smartuni/riot-po-2025/nodes/firmware/custom-modules/tables/tables.c

#include "include/tables.h"
#include <stdatomic.h>
#include <stdio.h>
#include <string.h>
#include <stdint.h>
#include "mutex.h"
#include <stddef.h>
#include "embUnit.h"
#include "embUnit/embUnit.h"
#include "fmt.h"
#include "cbor.h"
#include "container.h"
#include "atomic_utils.h"


// Return Codes
#define TABLE_ERROR_SIZE_TOO_BIG -1
#define TABLE_ERROR_INVALID_GATE_ID -2
#define TABLE_ERROR_NOT_FOUND   -3

// Static tables
static target_state_entry target_state_entry_table[MAX_GATE_COUNT];
static int target_state_entry_count = 0;
static is_state_entry is_state_entry_table[MAX_GATE_COUNT];
static int is_state_entry_count = 0;
static seen_status_entry seen_status_entry_table[MAX_GATE_COUNT][MAX_SENSE_COUNT];
static int seen_status_entry_count = 0;
static jobs_entry jobs_entry_table[MAX_GATE_COUNT];
static int jobs_entry_count = 0;
static timestamp_entry timestamp_table[MAX_GATE_COUNT];
static int timestamp_entry_count = 0;

static target_state_entry returnTargetTable[MAX_GATE_COUNT];
static is_state_entry returnIsTable[MAX_GATE_COUNT];
static seen_status_entry returnSeenTable[MAX_GATE_COUNT];
static jobs_entry returnJobsTable[MAX_GATE_COUNT];

// Mutexes for thread safety
static mutex_t target_state_mutex = MUTEX_INIT;
static mutex_t is_state_mutex = MUTEX_INIT;
static mutex_t seen_status_mutex = MUTEX_INIT;
static mutex_t jobs_mutex = MUTEX_INIT;
static mutex_t timestamp_mutex = MUTEX_INIT;
static mutex_t decode_mutex = MUTEX_INIT;

static volatile uint32_t device_timestamp = 0;

void increment_device_timestamp(void) {
    atomic_fetch_add_u32(&device_timestamp, 1);
}

uint32_t increment_and_get_device_timestamp(void) {
    return atomic_fetch_add_u32(&device_timestamp, 1);
}

uint32_t get_device_timestamp(void) {
    return atomic_load_u32(&device_timestamp);
}

/**
 * Initialize all tables with default values
 */
int init_tables(void) {
    mutex_lock(&target_state_mutex);
    mutex_lock(&is_state_mutex);
    mutex_lock(&seen_status_mutex);
    mutex_lock(&jobs_mutex);
    mutex_lock(&timestamp_mutex);
    
    for (int i = 0; i < MAX_GATE_COUNT; i++) {
        target_state_entry_table[i].gateID = MAX_GATE_COUNT;  // Mark as empty
        is_state_entry_table[i].gateID = MAX_GATE_COUNT;
        jobs_entry_table[i].gateID = MAX_GATE_COUNT;
        timestamp_table[i].gateID = MAX_GATE_COUNT;
    }

    for (int i = 0; i < MAX_GATE_COUNT; i++) {
        for (int j = 0; j < MAX_SENSE_COUNT; j++) {
            seen_status_entry_table[i][j].gateID = MAX_GATE_COUNT;
            seen_status_entry_table[i][j].senseMateID = MAX_SENSE_COUNT;
        }
    }
    
    mutex_unlock(&timestamp_mutex);
    mutex_unlock(&jobs_mutex);
    mutex_unlock(&seen_status_mutex);
    mutex_unlock(&is_state_mutex);
    mutex_unlock(&target_state_mutex);
    
    return TABLE_SUCCESS;
}

static int is_target_state_entry_present_internal(uint8_t gate_id) {
    if (gate_id >= MAX_GATE_COUNT) {
        return 0;  // Invalid gate_id = not present
    }
    uint8_t entry_gate_id = target_state_entry_table[gate_id].gateID;
    return entry_gate_id != MAX_GATE_COUNT && entry_gate_id == gate_id;
}

static int is_is_state_entry_present_internal(uint8_t gate_id) {
    if (gate_id >= MAX_GATE_COUNT) {
        return 0;
    }
    uint8_t entry_gate_id = is_state_entry_table[gate_id].gateID;
    return entry_gate_id != MAX_GATE_COUNT && entry_gate_id == gate_id;
}

static int is_seen_status_entry_present_internal(uint8_t gate_id, uint8_t sense_id) {
    if (gate_id >= MAX_GATE_COUNT || sense_id >= MAX_SENSE_COUNT) {
        return 0;
    }
    seen_status_entry entry = seen_status_entry_table[gate_id][sense_id];
    return entry.gateID != MAX_GATE_COUNT 
            && entry.gateID == gate_id 
            && entry.senseMateID != MAX_SENSE_COUNT 
            && entry.senseMateID == sense_id;
}

static int is_jobs_entry_present_internal(uint8_t gate_id) {
    if (gate_id >= MAX_GATE_COUNT) {
        return 0;
    }
    uint8_t entry_gate_id = jobs_entry_table[gate_id].gateID;
    return entry_gate_id != MAX_GATE_COUNT && entry_gate_id == gate_id;
}

static int is_timestamp_entry_present_internal(uint8_t gate_id) {
    if (gate_id >= MAX_GATE_COUNT) {
        return 0;
    }
    uint8_t entry_gate_id = timestamp_table[gate_id].gateID;
    return entry_gate_id != MAX_GATE_COUNT && entry_gate_id == gate_id;
}



static inline int is_valid_gate_id(uint8_t gate_id) {
    return gate_id < MAX_GATE_COUNT;
}

int target_state_table_to_cbor_test(target_state_entry table[], cbor_buffer* buffer) {
    CborEncoder encoder, arrayEncoder, entriesEncoder, singleEntryEncoder;
    cbor_encoder_init(&encoder, buffer->buffer, sizeof(uint8_t) * 100, 0);
    cbor_encoder_create_array(&encoder, &arrayEncoder, 3); // [
    cbor_encode_int(&arrayEncoder, TARGET_STATE_KEY); // Entry 1
    cbor_encode_int(&arrayEncoder, 2008); // Entry 2
    cbor_encoder_create_array(&arrayEncoder, &entriesEncoder, 4); // Entry 3

    // [Table Entry]
    for(int i = 0; i < 4; i++) {
        if (table[i].gateID != MAX_GATE_COUNT) {
            cbor_encoder_create_array(&entriesEncoder, &singleEntryEncoder, 3); // []
            cbor_encode_int(&singleEntryEncoder, table[i].gateID);
            cbor_encode_int(&singleEntryEncoder, table[i].state);
            cbor_encode_int(&singleEntryEncoder, table[i].timestamp);
            cbor_encoder_close_container(&entriesEncoder, &singleEntryEncoder); // ]
        }
    }

    cbor_encoder_close_container(&arrayEncoder, &entriesEncoder); // ]
    cbor_encoder_close_container(&encoder, &arrayEncoder); // ]

    buffer->cbor_size = (uint8_t) cbor_encoder_get_buffer_size (&encoder, buffer->buffer);

    return 0;
}

int target_state_table_to_cbor(cbor_buffer* buffer) {
    if (target_state_entry_count == 0){
        return -1; // No entries in table
    }
    CborEncoder encoder, arrayEncoder, entriesEncoder, singleEntryEncoder;
    cbor_encoder_init(&encoder, buffer->buffer, sizeof(uint8_t) * 100, 0);
    cbor_encoder_create_array(&encoder, &arrayEncoder, 2); // [
    cbor_encode_int(&arrayEncoder, TARGET_STATE_KEY); // Entry 1
    cbor_encoder_create_array(&arrayEncoder, &entriesEncoder, target_state_entry_count); // Entry 2

    // [Table Entry]
    for(int i = 0; i < MAX_GATE_COUNT; i++) {
        if (is_target_state_entry_present_internal(i)) {
            cbor_encoder_create_array(&entriesEncoder, &singleEntryEncoder, 3); // []
            cbor_encode_int(&singleEntryEncoder, target_state_entry_table[i].gateID);
            cbor_encode_int(&singleEntryEncoder, target_state_entry_table[i].state);
            cbor_encode_int(&singleEntryEncoder, target_state_entry_table[i].timestamp);
            cbor_encoder_close_container(&entriesEncoder, &singleEntryEncoder); // ]
        }
    }

    cbor_encoder_close_container(&arrayEncoder, &entriesEncoder); // ]
    cbor_encoder_close_container(&encoder, &arrayEncoder); // ]

    buffer->cbor_size =  (uint8_t) cbor_encoder_get_buffer_size (&encoder, buffer->buffer);

    return 0;
}

int is_state_table_to_cbor(cbor_buffer* buffer) {
    if (is_state_entry_count == 0){
        return -1; // No entries in table
    }
    CborEncoder encoder, arrayEncoder, entriesEncoder, singleEntryEncoder;
    cbor_encoder_init(&encoder, buffer->buffer, sizeof(uint8_t) * 100, 0);
    cbor_encoder_create_array(&encoder, &arrayEncoder, 2); // [
    cbor_encode_int(&arrayEncoder, TARGET_STATE_KEY); // Entry 1
    cbor_encoder_create_array(&arrayEncoder, &entriesEncoder, is_state_entry_count); // Entry 2

    // [Table Entry]
    for(int i = 0; i < MAX_GATE_COUNT; i++) {
        if(is_is_state_entry_present_internal(i)) {
            cbor_encoder_create_array(&entriesEncoder, &singleEntryEncoder, 3); // []
            cbor_encode_int(&singleEntryEncoder, is_state_entry_table[i].gateID);
            cbor_encode_int(&singleEntryEncoder, is_state_entry_table[i].state);
            cbor_encode_int(&singleEntryEncoder, is_state_entry_table[i].gateTime);
            cbor_encoder_close_container(&entriesEncoder, &singleEntryEncoder); // ]
        }
    }

    cbor_encoder_close_container(&arrayEncoder, &entriesEncoder); // ]
    cbor_encoder_close_container(&encoder, &arrayEncoder); // ]

    buffer->cbor_size =  (uint8_t) cbor_encoder_get_buffer_size (&encoder, buffer->buffer);

    return 0;
}

int seen_status_table_to_cbor(cbor_buffer* buffer) {
    if (seen_status_entry_count == 0){
        return -1; // No entries in table
    }
    CborEncoder encoder, arrayEncoder, entriesEncoder, singleEntryEncoder;
    cbor_encoder_init(&encoder, buffer->buffer, sizeof(uint8_t) * 100, 0);
    cbor_encoder_create_array(&encoder, &arrayEncoder, 2); // [
    cbor_encode_int(&arrayEncoder, TARGET_STATE_KEY); // Entry 1
    cbor_encoder_create_array(&arrayEncoder, &entriesEncoder, seen_status_entry_count); // Entry 2

    // [Table Entry]
    for(int i = 0; i < MAX_GATE_COUNT; i++) {
        for (int j = 0; j < MAX_SENSE_COUNT; j++) {
            if(is_seen_status_entry_present_internal(i, j)) {
                cbor_encoder_create_array(&entriesEncoder, &singleEntryEncoder, 3); // []
                cbor_encode_int(&singleEntryEncoder, seen_status_entry_table[i][j].gateID);
                cbor_encode_int(&singleEntryEncoder, seen_status_entry_table[i][j].gateTime);
                cbor_encode_int(&singleEntryEncoder, seen_status_entry_table[i][j].status);
                cbor_encode_int(&singleEntryEncoder, seen_status_entry_table[i][j].senseMateID);
                cbor_encoder_close_container(&entriesEncoder, &singleEntryEncoder); // ]
            }
        }
    }

    cbor_encoder_close_container(&arrayEncoder, &entriesEncoder); // ]
    cbor_encoder_close_container(&encoder, &arrayEncoder); // ]

    buffer->cbor_size =  (uint8_t) cbor_encoder_get_buffer_size (&encoder, buffer->buffer);

    return 0;
}

int jobs_table_to_cbor(cbor_buffer* buffer) {
    if (jobs_entry_count == 0){
        return -1; // No jobs in table
    }
    CborEncoder encoder, arrayEncoder, entriesEncoder, singleEntryEncoder;
    cbor_encoder_init(&encoder, buffer->buffer, sizeof(uint8_t) * 100, 0);
    cbor_encoder_create_array(&encoder, &arrayEncoder, 2); // [
    cbor_encode_int(&arrayEncoder, TARGET_STATE_KEY); // Entry 1
    cbor_encoder_create_array(&arrayEncoder, &entriesEncoder, jobs_entry_count); // Entry 2

    // [Table Entry]
    for(int i = 0; i < MAX_GATE_COUNT; i++) {
        if (is_jobs_entry_present_internal(i)) {
            cbor_encoder_create_array(&entriesEncoder, &singleEntryEncoder, 3); // []
            cbor_encode_int(&singleEntryEncoder, jobs_entry_table[i].gateID);
            cbor_encode_int(&singleEntryEncoder, jobs_entry_table[i].done);
            cbor_encoder_close_container(&entriesEncoder, &singleEntryEncoder); // ]
        }
    }

    cbor_encoder_close_container(&arrayEncoder, &entriesEncoder); // ]
    cbor_encoder_close_container(&encoder, &arrayEncoder); // ]

    buffer->cbor_size =  (uint8_t) cbor_encoder_get_buffer_size (&encoder, buffer->buffer);

    return 0;
}

int timestamp_table_to_cbor(cbor_buffer* buffer) {
    if (timestamp_entry_count == 0){
        return -1; // No jobs in table
    }
    CborEncoder encoder, arrayEncoder, entriesEncoder, singleEntryEncoder;
    cbor_encoder_init(&encoder, buffer->buffer, sizeof(uint8_t) * 100, 0);
    cbor_encoder_create_array(&encoder, &arrayEncoder, 2); // [
    cbor_encode_int(&arrayEncoder, TIMESTAMP_KEY); // Entry 1
    cbor_encoder_create_array(&arrayEncoder, &entriesEncoder, timestamp_entry_count); // Entry 2

    // [Table Entry]
    for(int i = 0; i < MAX_GATE_COUNT; i++) {
        if (is_jobs_entry_present_internal(i)) {
            cbor_encoder_create_array(&entriesEncoder, &singleEntryEncoder, 3); // []
            cbor_encode_int(&singleEntryEncoder, timestamp_table[i].gateID);
            cbor_encode_int(&singleEntryEncoder, timestamp_table[i].timestamp);
            cbor_encode_int(&singleEntryEncoder, timestamp_table[i].rssi);
            cbor_encoder_close_container(&entriesEncoder, &singleEntryEncoder); // ]
        }
    }

    cbor_encoder_close_container(&arrayEncoder, &entriesEncoder); // ]
    cbor_encoder_close_container(&encoder, &arrayEncoder); // ]

    buffer->cbor_size =  (uint8_t) cbor_encoder_get_buffer_size (&encoder, buffer->buffer);

    return 0;
}

 int print_target_table_test(void){
    printf("\n--- TARGET STATE TABLE ---\n");
    
    for (int i = 0; i < MAX_GATE_COUNT; i++) {
        if (target_state_entry_table[i].gateID!= MAX_GATE_COUNT) { // Entry ist valid
            printf("Gate: %d, State: %d, Time: %d\n", target_state_entry_table[i].gateID, target_state_entry_table[i].state, target_state_entry_table[i].timestamp);
        }
    }
    return 1;
}


int cbor_to_table_test(cbor_buffer* buffer, int8_t rssi) {
    CborParser parser;
    CborValue value;
    CborValue wrapperValue;
    CborValue fieldsValue;
    CborValue entryValue;
    mutex_lock(&decode_mutex);
    int tableType, timeStamp, typeOfSender, deviceID;
    memset(returnTargetTable, MAX_GATE_COUNT, sizeof(returnTargetTable));
    memset(returnIsTable, MAX_GATE_COUNT, sizeof(returnIsTable));
    memset(returnSeenTable, MAX_GATE_COUNT, sizeof(returnSeenTable));
    memset(returnJobsTable, MAX_GATE_COUNT, sizeof(returnJobsTable));

    if (buffer->cbor_size != 1) {
        mutex_unlock(&decode_mutex);
        return -1;
    }

    cbor_parser_init(buffer->buffer, buffer->package_size[0], 0, &parser, &value);

    if(cbor_value_enter_container(&value, &wrapperValue) != CborNoError) {
        mutex_unlock(&decode_mutex);
        return -30;
    }

    if(!cbor_value_is_integer(&wrapperValue) || cbor_value_get_int(&wrapperValue, &tableType) != CborNoError) {
        mutex_unlock(&decode_mutex);
        return -2;
    } // get type of table

    // get header information depending on table type
    switch (tableType)
    {
    case TARGET_STATE_KEY:
        cbor_value_advance(&wrapperValue);
        if(!cbor_value_is_integer(&wrapperValue) || cbor_value_get_int(&wrapperValue, &timeStamp) != CborNoError) {
            mutex_unlock(&decode_mutex);
            return -3;
        } // get timestamp
        cbor_value_advance(&wrapperValue);
        if(!cbor_value_is_integer(&wrapperValue) || cbor_value_get_int(&wrapperValue, &typeOfSender) != CborNoError) {
            mutex_unlock(&decode_mutex);
            return -4;
        } // get whether Sensemate, gate or Server sent msg
        cbor_value_advance(&wrapperValue);
        if(!cbor_value_is_integer(&wrapperValue) || cbor_value_get_int(&wrapperValue, &deviceID) != CborNoError) {
            mutex_unlock(&decode_mutex);
            return -5;
        } // get deviceID
        break;
    case IS_STATE_KEY:
        cbor_value_advance(&wrapperValue);
        if(!cbor_value_is_integer(&wrapperValue) || cbor_value_get_int(&wrapperValue, &timeStamp) != CborNoError) {
            mutex_unlock(&decode_mutex);
            return -6;
        } // get timestamp
        cbor_value_advance(&wrapperValue);
        if(!cbor_value_is_integer(&wrapperValue) || cbor_value_get_int(&wrapperValue, &typeOfSender) != CborNoError) {
            mutex_unlock(&decode_mutex);
            return -7;
        } // get whether Sensemate, gate or Server sent msg
        cbor_value_advance(&wrapperValue);
        if(!cbor_value_is_integer(&wrapperValue) || cbor_value_get_int(&wrapperValue, &deviceID) != CborNoError) {
            mutex_unlock(&decode_mutex);
            return -8;
        } // get deviceID
        break;
    case SEEN_STATUS_KEY:
    cbor_value_advance(&wrapperValue);
        if(!cbor_value_is_integer(&wrapperValue) || cbor_value_get_int(&wrapperValue, &timeStamp) != CborNoError) {
            mutex_unlock(&decode_mutex);
            return -9;
        } // get timestamp
        cbor_value_advance(&wrapperValue);
        if(!cbor_value_is_integer(&wrapperValue) || cbor_value_get_int(&wrapperValue, &typeOfSender) != CborNoError) {
            mutex_unlock(&decode_mutex);
            return -10;
        } // get whether Sensemate, gate or Server sent msg
        cbor_value_advance(&wrapperValue);
        if(!cbor_value_is_integer(&wrapperValue) || cbor_value_get_int(&wrapperValue, &deviceID) != CborNoError) {
            mutex_unlock(&decode_mutex);
            return -11;
        } // get deviceID
        break;
    case JOBS_KEY:
        // no further header information for JOBS table
        break;
    default:
        break;
    }

    // [ enter second container
    cbor_value_advance(&wrapperValue);
    if(cbor_value_enter_container(&wrapperValue, &fieldsValue) != CborNoError) {
        mutex_unlock(&decode_mutex);
        return -12;
    }
    
    int id, s, sID, p, gt;
    size_t length = 0;
    cbor_value_get_array_length(&wrapperValue, &length); 	
    for(size_t i = 0; i < length; i++) {
        cbor_value_enter_container(&fieldsValue, &entryValue); // [
        switch(tableType) {
            case TARGET_STATE_KEY:
                if(!cbor_value_is_integer(&entryValue) || cbor_value_get_int(&entryValue, &id) != CborNoError) {
                    mutex_unlock(&decode_mutex);
                    return -13;
                }
                cbor_value_advance(&entryValue);
                if(!cbor_value_is_integer(&entryValue) || cbor_value_get_int(&entryValue, &s) != CborNoError) {
                    mutex_unlock(&decode_mutex);
                    return -14;
                }
                cbor_value_advance(&entryValue);
                target_state_entry newTargetEntry = {id, s, timeStamp};
                returnTargetTable[i] = newTargetEntry;
                break;
            case IS_STATE_KEY:
                if(!cbor_value_is_integer(&entryValue) || cbor_value_get_int(&entryValue, &id) != CborNoError) {
                    mutex_unlock(&decode_mutex);
                    return -15;
                }
                cbor_value_advance(&entryValue);
                if(!cbor_value_is_integer(&entryValue) || cbor_value_get_int(&entryValue, &s) != CborNoError) {
                    mutex_unlock(&decode_mutex);
                    return -16;
                }
                cbor_value_advance(&entryValue);
                if(!cbor_value_is_integer(&entryValue) || cbor_value_get_int(&entryValue, &gt) != CborNoError) {
                    mutex_unlock(&decode_mutex);
                    return -17;
                }
                cbor_value_advance(&entryValue);
                is_state_entry newIsEntry = {id, s, gt};
                returnIsTable[i] = newIsEntry;
                break;
            case SEEN_STATUS_KEY:
                if(!cbor_value_is_integer(&entryValue) || cbor_value_get_int(&entryValue, &id) != CborNoError) {
                    mutex_unlock(&decode_mutex);
                    return -18;
                }
                cbor_value_advance(&entryValue);
                if(!cbor_value_is_integer(&entryValue) || cbor_value_get_int(&entryValue, &gt) != CborNoError) {
                    mutex_unlock(&decode_mutex);
                    return -19;
                }
                cbor_value_advance(&entryValue);
                if(!cbor_value_is_integer(&entryValue) || cbor_value_get_int(&entryValue, &s) != CborNoError) {
                    mutex_unlock(&decode_mutex);
                    return -20;
                }
                cbor_value_advance(&entryValue);
                if(!cbor_value_is_integer(&entryValue) || cbor_value_get_int(&entryValue, &sID) != CborNoError) {
                    mutex_unlock(&decode_mutex);
                    return -21;
                }
                cbor_value_advance(&entryValue);
                seen_status_entry newSeenEntry = {id, gt, s, sID};
                returnSeenTable[i] = newSeenEntry;
                break;
            case JOBS_KEY:
                if(!cbor_value_is_integer(&entryValue) || cbor_value_get_int(&entryValue, &id) != CborNoError) {
                    mutex_unlock(&decode_mutex);
                    return -22;
                }
                cbor_value_advance(&entryValue);
                if(!cbor_value_is_integer(&entryValue) || cbor_value_get_int(&entryValue, &p) != CborNoError) {
                    mutex_unlock(&decode_mutex);
                    return -23;
                }
                cbor_value_advance(&entryValue);
                jobs_entry newJobsEntry = {id, JOB_IN_PROGRESS, p};
                returnJobsTable[i] = newJobsEntry;
                break;
        }
        cbor_value_leave_container(&fieldsValue,&entryValue); // ]
    }

    cbor_value_leave_container(&wrapperValue, &fieldsValue); // ]	
    cbor_value_leave_container(&value, &wrapperValue); // ]	

    // Integrate local data into global table
    if(typeOfSender == GATE_NODE) {
        timestamp_entry change_entry = {deviceID, timeStamp, rssi};
        set_timestamp_entry(&change_entry);
    }

    int res = 0;
    switch(tableType) {
            case TARGET_STATE_KEY:
                res |= merge_target_state_entry_table(returnTargetTable, (length));
                break;
            case IS_STATE_KEY:
                res |= merge_is_state_entry_table(returnIsTable, (length));
                break;
            case SEEN_STATUS_KEY:
                res |= merge_seen_status_entry_table(returnSeenTable, (length));
                break;
            case JOBS_KEY:
                res |= merge_jobs_entry_table(returnJobsTable, (length));
                break;
            default:
                mutex_unlock(&decode_mutex);
                return -24;
    }
    
    mutex_unlock(&decode_mutex);
    return res;
}

int set_target_state_entry(const target_state_entry* entry) {
    if (entry == NULL) {
        return TABLE_ERROR_INVALID_GATE_ID;
    }
    
    uint8_t gate_id = entry->gateID;
    if (!is_valid_gate_id(gate_id)) {
        return TABLE_ERROR_INVALID_GATE_ID;
    }
    
    mutex_lock(&target_state_mutex);
    int res = TABLE_NO_UPDATES;
    if (!is_target_state_entry_present_internal(gate_id)) {
        // Entry doesn't exist yet, add it
        target_state_entry_count++;
        target_state_entry_table[gate_id] = *entry;
        res |= TABLE_NEW_RECORD;
    }
    else if (target_state_entry_table[gate_id].timestamp < entry->timestamp) {
        // New entry is newer, update ours
        target_state_entry_table[gate_id] = *entry;
        res |= TABLE_UPDATED;
    }
    
    mutex_unlock(&target_state_mutex);
    return res;
}

int set_is_state_entry(const is_state_entry* entry) {
    printf("Called: set_is_state_entry\n");
    if (entry == NULL) {
        return TABLE_ERROR_INVALID_GATE_ID;
    }
    
    uint8_t gate_id = entry->gateID;
    if (!is_valid_gate_id(gate_id)) {
        return TABLE_ERROR_INVALID_GATE_ID;
    }
    
    mutex_lock(&is_state_mutex);
    int res = TABLE_NO_UPDATES;
    if (!is_is_state_entry_present_internal(gate_id)) {
        // Entry doesn't exist yet, add it
        is_state_entry_count++;
        is_state_entry_table[gate_id] = *entry;
        res |= TABLE_NEW_RECORD;
    }
    else if (is_state_entry_table[gate_id].gateTime < entry->gateTime) {
        // New entry is newer, update ours
        is_state_entry_table[gate_id] = *entry;
        res |= TABLE_UPDATED;
    }
    
    mutex_unlock(&is_state_mutex);
    return res;
}

int set_seen_status_entry(const seen_status_entry* entry) {
    if (entry == NULL) {
        return TABLE_ERROR_INVALID_GATE_ID;
    }
    
    uint8_t gate_id = entry->gateID;
    uint8_t sense_id = entry->senseMateID;
    if (!is_valid_gate_id(gate_id)) {
        return TABLE_ERROR_INVALID_GATE_ID;
    }
    
    mutex_lock(&seen_status_mutex);
    int res = TABLE_NO_UPDATES;
    if (!is_seen_status_entry_present_internal(gate_id, sense_id)) {
        // Entry doesn't exist yet, add it
        seen_status_entry_count++;
        seen_status_entry_table[gate_id][sense_id] = *entry;
        res |= TABLE_NEW_RECORD;
    }
    else if (seen_status_entry_table[gate_id][sense_id].gateTime < entry->gateTime) {
        // New entry is newer, update ours
        seen_status_entry_table[gate_id][sense_id] = *entry;
        res |= TABLE_UPDATED;
    }
    
    mutex_unlock(&seen_status_mutex);
    return res;
}

int set_jobs_entry(const jobs_entry* entry) {
    if (entry == NULL) {
        return TABLE_ERROR_INVALID_GATE_ID;
    }
    
    uint8_t gate_id = entry->gateID;
    if (!is_valid_gate_id(gate_id)) {
        return TABLE_ERROR_INVALID_GATE_ID;
    }
    
    mutex_lock(&jobs_mutex);
    int res = TABLE_UPDATED;
    if (!is_jobs_entry_present_internal(gate_id)) {
        jobs_entry_count++;
        res |= TABLE_NEW_RECORD;
    }
    jobs_entry_table[gate_id] = *entry;
    mutex_unlock(&jobs_mutex);
    
    return res;
}

int set_timestamp_entry(const timestamp_entry* entry) {
    if (entry == NULL) {
        return TABLE_ERROR_INVALID_GATE_ID;
    }
    
    uint8_t gate_id = entry->gateID;
    if (!is_valid_gate_id(gate_id)) {
        return TABLE_ERROR_INVALID_GATE_ID;
    }
    
    mutex_lock(&timestamp_mutex);
    int res = TABLE_NO_UPDATES;
    if (!is_timestamp_entry_present_internal(gate_id)) {
        timestamp_entry_count++;
        res |= TABLE_NEW_RECORD;
    }
    else {
        res |= TABLE_UPDATED;
    }
    timestamp_table[gate_id] = *entry;
    mutex_unlock(&timestamp_mutex);
    
    return res;
}

int force_set_target_state_entry(const target_state_entry* entry) {
    if (entry == NULL) {
        return TABLE_ERROR_INVALID_GATE_ID;
    }
    
    uint8_t gate_id = entry->gateID;
    if (!is_valid_gate_id(gate_id)) {
        return TABLE_ERROR_INVALID_GATE_ID;
    }
    
    mutex_lock(&target_state_mutex);
    target_state_entry_table[gate_id] = *entry;
    mutex_unlock(&target_state_mutex);
    
    return TABLE_UPDATED;
}

int merge_target_state_entry_table(const target_state_entry* other, uint8_t size) {
    if (size >= MAX_GATE_COUNT) {
        return TABLE_ERROR_SIZE_TOO_BIG;
    }
    int merge_result = TARGET_STATE_TABLE_NO_UPDATES;
    for (int i = 0; i < size; i++) {
        int result = set_target_state_entry(&other[i]);
        if (TABLE_UPDATED == result || TABLE_NEW_RECORD == result) {
            merge_result |= result; 
        }
    }
    return merge_result;
}

int merge_is_state_entry_table(const is_state_entry* other, uint8_t size) {
    if (size >= MAX_GATE_COUNT) {
        return TABLE_ERROR_SIZE_TOO_BIG;
    }
    int merge_result = IS_STATE_TABLE_NO_UPDATES;
    for (int i = 0; i < size; i++) {
        int result = set_is_state_entry(&other[i]);
        if (TABLE_UPDATED == result || TABLE_NEW_RECORD == result) {
            merge_result |= result; 
        }
    }
    return merge_result;
}

int merge_seen_status_entry_table(const seen_status_entry* other, uint8_t size) {
    if (size >= MAX_GATE_COUNT) {
        return TABLE_ERROR_SIZE_TOO_BIG;
    }
    int merge_result = SEEN_STATUS_TABLE_NO_UPDATES;
    for (int i = 0; i < size; i++) {
        int result = set_seen_status_entry(&other[i]);
        if (TABLE_UPDATED == result || TABLE_NEW_RECORD == result) {
            merge_result |= result; 
        }
    }
    return merge_result;
}

int merge_timestamp_entry_table(const timestamp_entry* other, uint8_t size) {
    if (size >= MAX_GATE_COUNT) {
        return TABLE_ERROR_SIZE_TOO_BIG;
    }
    int merge_result = TIMESTAMP_TABLE_NO_UPDATES;
    for (int i = 0; i < size; i++) {
        int result = set_timestamp_entry(&other[i]);
        if (TABLE_UPDATED == result || TABLE_NEW_RECORD == result) {
            merge_result |= result; 
        }
    }
    return merge_result;
}

int merge_jobs_entry_table(const jobs_entry* other, uint8_t size) {
    if (size >= MAX_GATE_COUNT) {
        return TABLE_ERROR_SIZE_TOO_BIG;
    }
    int merge_result = JOBS_STATE_TABLE_NO_UPDATES;
    for (int i = 0; i < size; i++) {
        int result = set_jobs_entry(&other[i]);
        if (TABLE_UPDATED == result || TABLE_NEW_RECORD == result) {
            merge_result |= result; 
        }
    }
    return merge_result;
}

int get_target_state_entry(uint8_t gate_id, target_state_entry* entry) {
    if (entry == NULL || !is_valid_gate_id(gate_id)) {
        return TABLE_ERROR_INVALID_GATE_ID;
    }
    
    mutex_lock(&target_state_mutex);
    
    if (!is_target_state_entry_present_internal(gate_id)) {
        mutex_unlock(&target_state_mutex);
        return TABLE_ERROR_NOT_FOUND;
    }
    
    *entry = target_state_entry_table[gate_id];
    mutex_unlock(&target_state_mutex);
    
    return TABLE_SUCCESS;
}

int get_is_state_entry(uint8_t gate_id, is_state_entry* entry) {
    if (entry == NULL || !is_valid_gate_id(gate_id)) {
        return TABLE_ERROR_INVALID_GATE_ID;
    }
    
    mutex_lock(&is_state_mutex);
    
    if (!is_is_state_entry_present_internal(gate_id)) {
        mutex_unlock(&is_state_mutex);
        return TABLE_ERROR_NOT_FOUND;
    }
    
    *entry = is_state_entry_table[gate_id];
    mutex_unlock(&is_state_mutex);
    
    return TABLE_SUCCESS;
}

int get_seen_status_entry(uint8_t gate_id, uint8_t sense_id, seen_status_entry* entry) {
    if (entry == NULL || !is_valid_gate_id(gate_id)) {
        return TABLE_ERROR_INVALID_GATE_ID;
    }
    
    mutex_lock(&seen_status_mutex);
    
    if (!is_seen_status_entry_present_internal(gate_id, sense_id)) {
        mutex_unlock(&seen_status_mutex);
        return TABLE_ERROR_NOT_FOUND;
    }
    
    *entry = seen_status_entry_table[gate_id][sense_id];
    mutex_unlock(&seen_status_mutex);
    
    return TABLE_SUCCESS;
}

int get_jobs_entry(uint8_t gate_id, jobs_entry* entry) {
    if (entry == NULL || !is_valid_gate_id(gate_id)) {
        return TABLE_ERROR_INVALID_GATE_ID;
    }
    
    mutex_lock(&jobs_mutex);
    
    if (!is_jobs_entry_present_internal(gate_id)) {
        mutex_unlock(&jobs_mutex);
        return TABLE_ERROR_NOT_FOUND;
    }
    
    *entry = jobs_entry_table[gate_id];
    mutex_unlock(&jobs_mutex);
    
    return TABLE_SUCCESS;
}

int get_timestamp_entry(uint8_t gate_id, timestamp_entry* entry) {
    if (entry == NULL || !is_valid_gate_id(gate_id)) {
        return TABLE_ERROR_INVALID_GATE_ID;
    }
    
    mutex_lock(&timestamp_mutex);
    
    if (!is_timestamp_entry_present_internal(gate_id)) {
        mutex_unlock(&timestamp_mutex);
        return TABLE_ERROR_NOT_FOUND;
    }
    
    *entry = timestamp_table[gate_id];
    mutex_unlock(&timestamp_mutex);
    
    return TABLE_SUCCESS;
}

const target_state_entry* get_target_state_table(void) {
    return target_state_entry_table;
}

const is_state_entry* get_is_state_table(void) {
    return is_state_entry_table;
}

const seen_status_entry* get_seen_status_table(void) {
    return &seen_status_entry_table[0][0];
}

const jobs_entry* get_jobs_table(void) {
    return jobs_entry_table;
}
 
const timestamp_entry* get_timestamp_table(void) {
    return timestamp_table;
}

int target_state_table_to_cbor_many_test(target_state_entry table[], int package_size, cbor_buffer* buffer) {
    printf("Entered function\n");
    // Assert: given package_size big enough
    if(BASE_CBOR_BYTE_SIZE + CBOR_TARGET_STATE_MAX_BYTE_SIZE > package_size) {
        printf("ASSERT failed. Size passed too small for cbor!\n");
        printf("%d + %d < %d\n", BASE_CBOR_BYTE_SIZE, CBOR_TARGET_STATE_MAX_BYTE_SIZE, package_size);
        return -1;
    }

    int no_cbor_packages = 0;
    int cbor_stream_index = 0;
    int size_of_current_cbor = 0;
    int table_index = 0;
    printf("This is the buffer: %p\n", buffer->buffer);
    while(table_index < 4) {
        printf("enterd while, i = %d, size = %d\n", table_index, size_of_current_cbor);
        CborEncoder encoder, arrayEncoder, entriesEncoder, singleEntryEncoder;
        uint8_t* space = (buffer->buffer) + (cbor_stream_index * sizeof(uint8_t));
        printf("Space = %p\n", space);
        printf("CBOR Index = %d\n", cbor_stream_index);
        cbor_encoder_init(&encoder, space, sizeof(uint8_t) * package_size, 0);
        cbor_encoder_create_array(&encoder, &arrayEncoder, 2); // [
        cbor_encode_int(&arrayEncoder, TARGET_STATE_KEY); // Entry 1
        cbor_encoder_create_array(&arrayEncoder, &entriesEncoder, 6); // Entry 2
        printf("while %d + %d < %d\n", size_of_current_cbor, CBOR_TARGET_STATE_MAX_BYTE_SIZE, package_size);
        while(size_of_current_cbor + CBOR_TARGET_STATE_MAX_BYTE_SIZE < package_size) {
            //validate table entry
            if(table[table_index].gateID != MAX_GATE_COUNT) {
                cbor_encoder_create_array(&entriesEncoder, &singleEntryEncoder, 3); // []
                cbor_encode_int(&singleEntryEncoder, table[table_index].gateID);
                cbor_encode_int(&singleEntryEncoder, table[table_index].state);
                cbor_encode_int(&singleEntryEncoder, table[table_index].timestamp);
                cbor_encoder_close_container(&entriesEncoder, &singleEntryEncoder); // ]
            }
            table_index++;
            size_of_current_cbor = (uint8_t) cbor_encoder_get_buffer_size (&entriesEncoder, space);
            printf("Entered one entry, size = %d\n", size_of_current_cbor);
        }
        cbor_encoder_close_container(&arrayEncoder, &entriesEncoder); // ]
        cbor_encoder_close_container(&encoder, &arrayEncoder); // ]
        cbor_stream_index += size_of_current_cbor;
        buffer->package_size[no_cbor_packages] = (uint8_t) size_of_current_cbor;
        no_cbor_packages++;
        size_of_current_cbor = 0;
    }
    buffer->cbor_size = no_cbor_packages;
    return no_cbor_packages;
}

int target_state_table_to_cbor_many(int package_size, cbor_buffer* buffer) {
    // Assert: given package_size big enough
    if(BASE_CBOR_BYTE_SIZE + CBOR_TARGET_STATE_MAX_BYTE_SIZE > package_size) {
        printf("ASSERT failed. Size passed too small for cbor!\n");
        return -1;
    }

    int no_cbor_packages = 0;
    int cbor_stream_index = 0;
    int size_of_current_cbor = 0;
    int table_index = 0;
    while((target_state_entry_count > 0) && (table_index < MAX_GATE_COUNT)) {
        CborEncoder encoder, arrayEncoder, entriesEncoder, singleEntryEncoder;
        uint8_t* space = (buffer->buffer) + (cbor_stream_index * sizeof(uint8_t));
        cbor_encoder_init(&encoder, space, sizeof(uint8_t) * package_size, 0);
        cbor_encoder_create_array(&encoder, &arrayEncoder, 5); // [
        cbor_encode_int(&arrayEncoder, TARGET_STATE_KEY); // Entry 1
        cbor_encode_int(&arrayEncoder, device_timestamp); // Entry 2
        cbor_encode_int(&arrayEncoder, DEVICE_TYPE); // Entry 3
        cbor_encode_int(&arrayEncoder, DEVICE_ID); // Entry 4
        cbor_encoder_create_array(&arrayEncoder, &entriesEncoder, target_state_entry_count); // Entry 5
        while((size_of_current_cbor + CBOR_TARGET_STATE_MAX_BYTE_SIZE < package_size) && (table_index < MAX_GATE_COUNT)) {
            if (target_state_entry_table[table_index].gateID != MAX_GATE_COUNT) {
                printf("Valid entry: %d\n", target_state_entry_table[table_index].gateID);
                cbor_encoder_create_array(&entriesEncoder, &singleEntryEncoder, 3); // []
                cbor_encode_int(&singleEntryEncoder, target_state_entry_table[table_index].gateID);
                cbor_encode_int(&singleEntryEncoder, target_state_entry_table[table_index].state);
                cbor_encode_int(&singleEntryEncoder, target_state_entry_table[table_index].timestamp);
                cbor_encoder_close_container(&entriesEncoder, &singleEntryEncoder); // ]
            }
            table_index++;
            size_of_current_cbor = (uint8_t) cbor_encoder_get_buffer_size (&entriesEncoder, space);
        }
        cbor_encoder_close_container(&arrayEncoder, &entriesEncoder); // ]
        cbor_encoder_close_container(&encoder, &arrayEncoder); // ]
        cbor_stream_index += size_of_current_cbor;
        buffer->package_size[no_cbor_packages] = (uint8_t) size_of_current_cbor;
        no_cbor_packages++;
        size_of_current_cbor = 0;
    }
    buffer->cbor_size = no_cbor_packages;
    return no_cbor_packages;
}

int is_state_table_to_cbor_many(int package_size, cbor_buffer* buffer) {
    // Assert: given package_size big enough
    if(BASE_CBOR_BYTE_SIZE + CBOR_IS_STATE_MAX_BYTE_SIZE > package_size) {
        printf("ASSERT failed. Size passed too small for cbor!\n");
        return -1;
    }

    int no_cbor_packages = 0;
    int cbor_stream_index = 0;
    int size_of_current_cbor = 0;
    int table_index = 0;
    int is_states_entry_processed = 0;
    int calculated_array_entries = (package_size - BASE_CBOR_BYTE_SIZE) / CBOR_IS_STATE_MAX_BYTE_SIZE;

    while((is_state_entry_count > 0) && (table_index < MAX_GATE_COUNT) && (is_state_entry_count - is_states_entry_processed) > 0) {
        CborEncoder encoder, arrayEncoder, entriesEncoder, singleEntryEncoder;
        uint8_t* space = (buffer->buffer) + (cbor_stream_index * sizeof(uint8_t));
        int i = 0;
        while( (i < calculated_array_entries) && (table_index < MAX_GATE_COUNT) && (is_state_entry_count - is_states_entry_processed) > 0) {
            // Create new package if needed
            if(size_of_current_cbor == 0 ){
                cbor_encoder_init(&encoder, space, sizeof(uint8_t) * package_size, 0);
                cbor_encoder_create_array(&encoder, &arrayEncoder, 5); // [
                cbor_encode_int(&arrayEncoder, IS_STATE_KEY); //Entry 1
                cbor_encode_int(&arrayEncoder, device_timestamp); // Entry 2
                cbor_encode_int(&arrayEncoder, DEVICE_TYPE); // Entry 3
                cbor_encode_int(&arrayEncoder, DEVICE_ID); // Entry 4
                if(is_state_entry_count - is_states_entry_processed < calculated_array_entries){
                    cbor_encoder_create_array(&arrayEncoder, &entriesEncoder, is_state_entry_count - is_states_entry_processed);  
                }else{
                    cbor_encoder_create_array(&arrayEncoder, &entriesEncoder, calculated_array_entries); 
                }
            } // Entry 1
            if (is_state_entry_table[table_index].gateID != MAX_GATE_COUNT) {
                cbor_encoder_create_array(&entriesEncoder, &singleEntryEncoder, 3); // []
                cbor_encode_int(&singleEntryEncoder, is_state_entry_table[table_index].gateID);
                cbor_encode_int(&singleEntryEncoder, is_state_entry_table[table_index].state);
                cbor_encode_int(&singleEntryEncoder, is_state_entry_table[table_index].gateTime);
                cbor_encoder_close_container(&entriesEncoder, &singleEntryEncoder); // ]
                is_states_entry_processed++;
                i++;
            }
            table_index++;
            size_of_current_cbor = (uint8_t) cbor_encoder_get_buffer_size (&entriesEncoder, space);
        }
        cbor_encoder_close_container(&arrayEncoder, &entriesEncoder); // ]
        cbor_encoder_close_container(&encoder, &arrayEncoder); // ]
        cbor_stream_index += size_of_current_cbor;
        buffer->package_size[no_cbor_packages] = (uint8_t) size_of_current_cbor;
        no_cbor_packages++;
        size_of_current_cbor = 0;
    }
    buffer->cbor_size = no_cbor_packages;
    return no_cbor_packages;
}

int is_state_table_to_cbor_many_to_server(int package_size, cbor_buffer* buffer) {
    // Assert: given package_size big enough
    if(BASE_CBOR_BYTE_SIZE + CBOR_IS_STATE_MAX_BYTE_SIZE > package_size) {
        printf("ASSERT failed. Size passed too small for cbor!\n");
        return -1;
    }

    int no_cbor_packages = 0;
    int cbor_stream_index = 0;
    int size_of_current_cbor = 0;
    int table_index = 0;
    int is_states_entry_processed = 0;
    int calculated_array_entries = (package_size - BASE_CBOR_BYTE_SIZE) / CBOR_IS_STATE_MAX_BYTE_SIZE;

    while((is_state_entry_count > 0) && (table_index < MAX_GATE_COUNT) && (is_state_entry_count - is_states_entry_processed) > 0) {
        CborEncoder encoder, arrayEncoder, entriesEncoder, singleEntryEncoder;
        uint8_t* space = (buffer->buffer) + (cbor_stream_index * sizeof(uint8_t));
        int i = 0;
        while( (i < calculated_array_entries) && (table_index < MAX_GATE_COUNT) && (is_state_entry_count - is_states_entry_processed) > 0) {
            // Create new package if needed
            if(size_of_current_cbor == 0 ){
                cbor_encoder_init(&encoder, space, sizeof(uint8_t) * package_size, 0);
                cbor_encoder_create_array(&encoder, &arrayEncoder, 2); // [
                cbor_encode_int(&arrayEncoder, IS_STATE_KEY);
                if(is_state_entry_count - is_states_entry_processed < calculated_array_entries){
                    cbor_encoder_create_array(&arrayEncoder, &entriesEncoder, is_state_entry_count - is_states_entry_processed);  
                }else{
                    cbor_encoder_create_array(&arrayEncoder, &entriesEncoder, calculated_array_entries); 
                }
            } // Entry 1
            if (is_state_entry_table[table_index].gateID != MAX_GATE_COUNT) {
                cbor_encoder_create_array(&entriesEncoder, &singleEntryEncoder, 3); // []
                cbor_encode_int(&singleEntryEncoder, is_state_entry_table[table_index].gateID);
                cbor_encode_int(&singleEntryEncoder, is_state_entry_table[table_index].state);
                cbor_encode_int(&singleEntryEncoder, is_state_entry_table[table_index].gateTime);
                cbor_encoder_close_container(&entriesEncoder, &singleEntryEncoder); // ]
                is_states_entry_processed++;
                i++;
            }
            table_index++;
            size_of_current_cbor = (uint8_t) cbor_encoder_get_buffer_size (&entriesEncoder, space);
        }
        cbor_encoder_close_container(&arrayEncoder, &entriesEncoder); // ]
        cbor_encoder_close_container(&encoder, &arrayEncoder); // ]
        cbor_stream_index += size_of_current_cbor;
        buffer->package_size[no_cbor_packages] = (uint8_t) size_of_current_cbor;
        no_cbor_packages++;
        size_of_current_cbor = 0;
    }
    buffer->cbor_size = no_cbor_packages;
    return no_cbor_packages;
}

int seen_status_table_to_cbor_many(int package_size, cbor_buffer* buffer) {
    /* Assert: given package_size big enough */
    if(BASE_CBOR_BYTE_SIZE + CBOR_SEEN_STATUS_MAX_BYTE_SIZE > package_size) {
        printf("ASSERT failed. Size passed too small for cbor!\n");
        return -1;
    }

    int no_cbor_packages = 0;
    int cbor_stream_index = 0;
    int size_of_current_cbor = 0;
    int table_index = 0; // GateMate index
    int sense_index = 0; // SenseMate index
    int seen_status_entry_processed = 0;
    int calculated_array_entries = (package_size - BASE_CBOR_BYTE_SIZE) / CBOR_SEEN_STATUS_MAX_BYTE_SIZE;

    while((seen_status_entry_count > 0) && (table_index < MAX_GATE_COUNT) && (seen_status_entry_count - seen_status_entry_processed) > 0) {
        CborEncoder encoder, arrayEncoder, entriesEncoder, singleEntryEncoder;
        uint8_t* space = (buffer->buffer) + (cbor_stream_index * sizeof(uint8_t));
        int entry_index = 0;
        while((entry_index < calculated_array_entries) && (table_index < MAX_GATE_COUNT) && (seen_status_entry_count - seen_status_entry_processed) > 0) {
            // Create new package if needed
            if(size_of_current_cbor == 0) {
                cbor_encoder_init(&encoder, space, sizeof(uint8_t) * package_size, 0);
                cbor_encoder_create_array(&encoder, &arrayEncoder, 5);        // [
                cbor_encode_int(&arrayEncoder, SEEN_STATUS_KEY);              // Entry 1
                cbor_encode_int(&arrayEncoder, device_timestamp); // Entry 2
                cbor_encode_int(&arrayEncoder, DEVICE_TYPE); // Entry 3
                cbor_encode_int(&arrayEncoder, DEVICE_ID); // Entry 4
                if(seen_status_entry_count - seen_status_entry_processed < calculated_array_entries) {
                    cbor_encoder_create_array(&arrayEncoder, &entriesEncoder, seen_status_entry_count - seen_status_entry_processed);
                }else {
                    cbor_encoder_create_array(&arrayEncoder, &entriesEncoder, calculated_array_entries);
                }
            }
            // Check all SenseMates of the current GateMate
            while((entry_index < calculated_array_entries) && (sense_index < MAX_SENSE_COUNT) && (seen_status_entry_count - seen_status_entry_processed) > 0) {
                if(seen_status_entry_table[table_index][sense_index].gateID != MAX_GATE_COUNT) {
                    cbor_encoder_create_array(&entriesEncoder, &singleEntryEncoder, 4); // []
                    cbor_encode_int(&singleEntryEncoder, seen_status_entry_table[table_index][sense_index].gateID);
                    cbor_encode_int(&singleEntryEncoder, seen_status_entry_table[table_index][sense_index].gateTime);
                    cbor_encode_int(&singleEntryEncoder, seen_status_entry_table[table_index][sense_index].status);
                    cbor_encode_int(&singleEntryEncoder, seen_status_entry_table[table_index][sense_index].senseMateID);
                    cbor_encoder_close_container(&entriesEncoder, &singleEntryEncoder);   // ]
                    seen_status_entry_processed++;
                    entry_index++;
                }
                sense_index++;

                // Get current size of CBOR package, if the package is full, break out of SenseMate loop
                size_of_current_cbor = (uint8_t) cbor_encoder_get_buffer_size (&entriesEncoder, space);
                if(size_of_current_cbor + CBOR_SEEN_STATUS_MAX_BYTE_SIZE >= package_size) {
                    break; // Paket full, break out of SenseMate loop
                }
            } /* while sense_index */

            if(sense_index == MAX_SENSE_COUNT) {
                table_index++; // Next GateMate
                sense_index = 0; // Reset SenseMate index
            }
        } /* while entry_index */

        // Close CBOR containers, write size to buffer and prepare for next package
        cbor_encoder_close_container(&arrayEncoder, &entriesEncoder); // ]
        cbor_encoder_close_container(&encoder, &arrayEncoder);        // ]
        cbor_stream_index += size_of_current_cbor;
        buffer->package_size[no_cbor_packages] = (uint8_t) size_of_current_cbor;
        no_cbor_packages++;
        size_of_current_cbor = 0;
    } /* while table_index */

    buffer->cbor_size = no_cbor_packages;
    return no_cbor_packages;
}

int seen_status_table_to_cbor_many_to_server(int package_size, cbor_buffer* buffer) {
    /* Assert: given package_size big enough */
    if(BASE_CBOR_BYTE_SIZE + CBOR_SEEN_STATUS_MAX_BYTE_SIZE > package_size) {
        printf("ASSERT failed. Size passed too small for cbor!\n");
        return -1;
    }

    int no_cbor_packages = 0;
    int cbor_stream_index = 0;
    int size_of_current_cbor = 0;
    int table_index = 0; // GateMate index
    int sense_index = 0; // SenseMate index
    int seen_status_entry_processed = 0;
    int calculated_array_entries = (package_size - BASE_CBOR_BYTE_SIZE) / CBOR_SEEN_STATUS_MAX_BYTE_SIZE;

    while((seen_status_entry_count > 0) && (table_index < MAX_GATE_COUNT) && (seen_status_entry_count - seen_status_entry_processed) > 0) {
        CborEncoder encoder, arrayEncoder, entriesEncoder, singleEntryEncoder;
        uint8_t* space = (buffer->buffer) + (cbor_stream_index * sizeof(uint8_t));
        int entry_index = 0;
        while((entry_index < calculated_array_entries) && (table_index < MAX_GATE_COUNT) && (seen_status_entry_count - seen_status_entry_processed) > 0) {
            // Create new package if needed
            if(size_of_current_cbor == 0) {
                cbor_encoder_init(&encoder, space, sizeof(uint8_t) * package_size, 0);
                cbor_encoder_create_array(&encoder, &arrayEncoder, 2);        // [
                cbor_encode_int(&arrayEncoder, SEEN_STATUS_KEY);              // Entry 1
                if(seen_status_entry_count - seen_status_entry_processed < calculated_array_entries) {
                    cbor_encoder_create_array(&arrayEncoder, &entriesEncoder, seen_status_entry_count - seen_status_entry_processed);
                }else {
                    cbor_encoder_create_array(&arrayEncoder, &entriesEncoder, calculated_array_entries);
                }
            }
            // Check all SenseMates of the current GateMate
            while((entry_index < calculated_array_entries) && (sense_index < MAX_SENSE_COUNT) && (seen_status_entry_count - seen_status_entry_processed) > 0) {
                if(seen_status_entry_table[table_index][sense_index].gateID != MAX_GATE_COUNT) {
                    cbor_encoder_create_array(&entriesEncoder, &singleEntryEncoder, 4); // []
                    cbor_encode_int(&singleEntryEncoder, seen_status_entry_table[table_index][sense_index].gateID);
                    cbor_encode_int(&singleEntryEncoder, seen_status_entry_table[table_index][sense_index].gateTime);
                    cbor_encode_int(&singleEntryEncoder, seen_status_entry_table[table_index][sense_index].status);
                    cbor_encode_int(&singleEntryEncoder, seen_status_entry_table[table_index][sense_index].senseMateID);
                    cbor_encoder_close_container(&entriesEncoder, &singleEntryEncoder);   // ]
                    seen_status_entry_processed++;
                    entry_index++;
                }
                sense_index++;

                // Get current size of CBOR package, if the package is full, break out of SenseMate loop
                size_of_current_cbor = (uint8_t) cbor_encoder_get_buffer_size (&entriesEncoder, space);
                if(size_of_current_cbor + CBOR_SEEN_STATUS_MAX_BYTE_SIZE >= package_size) {
                    break; // Paket full, break out of SenseMate loop
                }
            } /* while sense_index */

            if(sense_index == MAX_SENSE_COUNT) {
                table_index++; // Next GateMate
                sense_index = 0; // Reset SenseMate index
            }
        } /* while entry_index */

        // Close CBOR containers, write size to buffer and prepare for next package
        cbor_encoder_close_container(&arrayEncoder, &entriesEncoder); // ]
        cbor_encoder_close_container(&encoder, &arrayEncoder);        // ]
        cbor_stream_index += size_of_current_cbor;
        buffer->package_size[no_cbor_packages] = (uint8_t) size_of_current_cbor;
        no_cbor_packages++;
        size_of_current_cbor = 0;
    } /* while table_index */

    buffer->cbor_size = no_cbor_packages;
    return no_cbor_packages;
}


int jobs_table_to_cbor_many(int package_size, cbor_buffer* buffer) {
    /* Assert: package_size big enough for at least one element */
    if (BASE_CBOR_BYTE_SIZE + CBOR_JOBS_MAX_BYTE_SIZE > package_size) {
        printf("ASSERT failed. Size passed too small for cbor!\n");
        return -1;
    }

    int no_cbor_packages = 0;
    int cbor_stream_index = 0;
    int size_of_current_cbor = 0;
    int table_index = 0;
    int jobs_entry_processed = 0;
    const int calculated_array_entries = (package_size - BASE_CBOR_BYTE_SIZE) / CBOR_JOBS_MAX_BYTE_SIZE;

    while ((jobs_entry_count > 0) && (table_index < MAX_GATE_COUNT) && (jobs_entry_count - jobs_entry_processed) > 0) {
        CborEncoder encoder, arrayEncoder, entriesEncoder, singleEntryEncoder;
        uint8_t* space = buffer->buffer + cbor_stream_index;
        int entry_index = 0;
        while ((entry_index < calculated_array_entries) && (table_index < MAX_GATE_COUNT) && (jobs_entry_count - jobs_entry_processed) > 0) {
            // Create new package if needed
            if (size_of_current_cbor == 0) {
                cbor_encoder_init(&encoder, space, package_size, 0);
                cbor_encoder_create_array(&encoder, &arrayEncoder, 2);          // [
                cbor_encode_int(&arrayEncoder, JOBS_KEY);                       // Entry 1
                cbor_encode_int(&arrayEncoder, device_timestamp); // Entry 2
                cbor_encode_int(&arrayEncoder, DEVICE_TYPE); // Entry 3
                cbor_encode_int(&arrayEncoder, DEVICE_ID); // Entry 4
                if(jobs_entry_count - jobs_entry_processed < calculated_array_entries){
                    cbor_encoder_create_array(&arrayEncoder, &entriesEncoder, jobs_entry_count - jobs_entry_processed);  
                }else{
                    cbor_encoder_create_array(&arrayEncoder, &entriesEncoder, calculated_array_entries); 
                }
            }
            if (jobs_entry_table[table_index].gateID != MAX_GATE_COUNT) {
                cbor_encoder_create_array(&entriesEncoder, &singleEntryEncoder, 2); // []
                cbor_encode_int(&singleEntryEncoder, jobs_entry_table[table_index].gateID);
                cbor_encode_int(&singleEntryEncoder, jobs_entry_table[table_index].done);
                cbor_encoder_close_container(&entriesEncoder, &singleEntryEncoder); // ]
                jobs_entry_processed++;
                entry_index++;
            }
            table_index++;
            size_of_current_cbor = (uint8_t)cbor_encoder_get_buffer_size(&entriesEncoder, space);
        } /* while entry_index */

        // Close package
        cbor_encoder_close_container(&arrayEncoder, &entriesEncoder); // ]
        cbor_encoder_close_container(&encoder,      &arrayEncoder);   // ]
        cbor_stream_index += size_of_current_cbor;
        buffer->package_size[no_cbor_packages++] = (uint8_t)size_of_current_cbor;
        size_of_current_cbor = 0;
    }
    buffer->cbor_size = no_cbor_packages;
    return no_cbor_packages;
}

int timestamp_table_to_cbor_many(int package_size, cbor_buffer* buffer) {
    /* Assert: package_size big enough for at least one element */
    if (BASE_CBOR_BYTE_SIZE + CBOR_TIMESTAMP_MAX_BYTE_SIZE > package_size) {
        printf("ASSERT failed. Size passed too small for cbor!\n");
        return -1;
    }

    int no_cbor_packages = 0;
    int cbor_stream_index = 0;
    int size_of_current_cbor = 0;
    int table_index = 0;
    int timestamp_entry_processed = 0;
    const int calculated_array_entries = (package_size - BASE_CBOR_BYTE_SIZE) / CBOR_TIMESTAMP_MAX_BYTE_SIZE;

    while ((timestamp_entry_count > 0) && (table_index  < MAX_GATE_COUNT) && (timestamp_entry_count - timestamp_entry_processed) > 0) {
        CborEncoder encoder, arrayEncoder, entriesEncoder, singleEntryEncoder;
        uint8_t* space = (buffer->buffer) + (cbor_stream_index * sizeof(uint8_t));
        int entry_index = 0;
        while ((entry_index < calculated_array_entries) && (table_index  < MAX_GATE_COUNT) && (timestamp_entry_count - timestamp_entry_processed) > 0) {
            // Create new package if needed
            if (size_of_current_cbor == 0) {
                cbor_encoder_init(&encoder, space, package_size, 0);
                cbor_encoder_create_array(&encoder, &arrayEncoder, 2);           // [
                cbor_encode_int(&arrayEncoder, TIMESTAMP_KEY);                  // Entry 1
                cbor_encode_int(&arrayEncoder, device_timestamp); // Entry 2
                cbor_encode_int(&arrayEncoder, DEVICE_TYPE); // Entry 3
                cbor_encode_int(&arrayEncoder, DEVICE_ID); // Entry 4
                if(timestamp_entry_count - timestamp_entry_processed < calculated_array_entries){
                    cbor_encoder_create_array(&arrayEncoder, &entriesEncoder, timestamp_entry_count - timestamp_entry_processed);  
                }else{
                    cbor_encoder_create_array(&arrayEncoder, &entriesEncoder, calculated_array_entries); 
                }
            }
            if (timestamp_table[table_index].gateID != MAX_GATE_COUNT) {
                cbor_encoder_create_array(&entriesEncoder, &singleEntryEncoder, 3); // []
                cbor_encode_int(&singleEntryEncoder, timestamp_table[table_index].gateID);
                cbor_encode_int(&singleEntryEncoder, timestamp_table[table_index].timestamp);
                cbor_encode_int(&singleEntryEncoder, timestamp_table[table_index].rssi);
                cbor_encoder_close_container(&entriesEncoder, &singleEntryEncoder); // ]
                timestamp_entry_processed++;
                entry_index++;
            }
            table_index++;
            size_of_current_cbor = (uint8_t) cbor_encoder_get_buffer_size(&entriesEncoder, space);
        } /* while entry_index */

       // Close package
        cbor_encoder_close_container(&arrayEncoder, &entriesEncoder); // ]
        cbor_encoder_close_container(&encoder,      &arrayEncoder);   // ]
        cbor_stream_index += size_of_current_cbor;
        buffer->package_size[no_cbor_packages++] = (uint8_t) size_of_current_cbor;
        size_of_current_cbor = 0;
    }
    buffer->cbor_size = no_cbor_packages;
    return no_cbor_packages;
}
