smartuni/riot-po-2025/nodes/firmware/senseMate/new_menu.c

#include "include/new_menu.h"
#include <string.h>
#include <tables.h>
#include <stdio.h>
#include "include/displayDemo.h"
#include "mate_lorawan.h"
#include "include/soundModule.h"
#include "event.h"
//#include "event/timeout.h"
#include "event/thread.h"
#define MAX_GATES MAX_GATE_COUNT
#define MAX_SENSE_MATES MAX_SENSE_COUNT
#define MIN_SIGNAL_STRENGTH -80
#define MIN_JOB_PRIO 1
#define SENSEMATE_ID DEVICE_ID

/*sorted by gate_id*/
gate_entry all_entries [MAX_GATES];
int current_num_gates = 0;

/*sorted by sig_strength, high to low*/
gate_entry *close_by_order [MAX_GATES];
int current_num_close_by = 0;

/*sorted by job_prio high to low*/
gate_entry *jobs_order [MAX_GATES];
int current_num_jobs = 0;


//upper and lower field on Display
display_entry upper_entry;
display_entry lower_entry;


//tables module buffer:
target_state_entry target_state_tbl_entry_buf;
is_state_entry is_state_tbl_entry_buf;
seen_status_entry seen_status_tbl_entry_buf;
jobs_entry jobs_tbl_entry_buf;
timestamp_entry timestamp_tbl_entry_buf;


void in_tables_set_gate_open_closed(int gate_id, gate_state state){
    if(get_timestamp_entry(gate_id, &timestamp_tbl_entry_buf) != TABLE_SUCCESS){
        return; //no timestamp entry found
    }
    timestamp_tbl_entry_buf.timestamp++;

    set_timestamp_entry(&(timestamp_entry){
        .gateID = gate_id,
        .timestamp = timestamp_tbl_entry_buf.timestamp,
        .rssi = timestamp_tbl_entry_buf.rssi
    });

    set_seen_status_entry(&(seen_status_entry){
        .gateID = gate_id,
        .status = state,
        .senseMateID = SENSEMATE_ID,
        .gateTime = timestamp_tbl_entry_buf.timestamp
    });
};

void in_tables_set_gate_job_done(int gate_id, bool done){
    if(get_jobs_entry(gate_id, &jobs_tbl_entry_buf) != TABLE_SUCCESS){
        return; //no jobs entry found
    }

    set_jobs_entry(&(jobs_entry){
        .gateID = gate_id,
        .done = done ? JOB_DONE : JOB_IN_PROGRESS,
        .priority = jobs_tbl_entry_buf.priority
    });
};

void update_with_target(int potential_id){
    if(get_target_state_entry(potential_id, &target_state_tbl_entry_buf) == TABLE_SUCCESS){
        //check if gate already there
        if(!gate_listed(target_state_tbl_entry_buf.gateID)){
            add_gate(&(gate_entry){
                .gate_id = target_state_tbl_entry_buf.gateID,
                .gate_is_state = UNKNOWN,
                .gate_requested_state = target_state_tbl_entry_buf.state,
                .job_is_todo = false,
                .job_prio = 0,
                .sig_strength = 0
            });
        }else{
            //update requested state
            set_requested_state(target_state_tbl_entry_buf.gateID, target_state_tbl_entry_buf.state);
        }
    }
}

void update_with_is_state(int potential_id){
    if(get_is_state_entry(potential_id, &is_state_tbl_entry_buf) == TABLE_SUCCESS){
        //check if gate already there
        if(!gate_listed(is_state_tbl_entry_buf.gateID)){
            add_gate(&(gate_entry){
                .gate_id = is_state_tbl_entry_buf.gateID,
                .gate_is_state = is_state_tbl_entry_buf.state,
                .gate_requested_state = UNKNOWN,
                .job_is_todo = false,
                .job_prio = 0,
                .sig_strength = 0
            });
        }else{
            //update is state
            set_is_state(is_state_tbl_entry_buf.gateID, is_state_tbl_entry_buf.state);
        }
    }
}

void update_with_seen_status(int potential_id){
    int timestamp = 0; 
    uint8_t state = 0;
    bool success = false;
    //get the latest seen status entry
    for (int i = 0; i < MAX_SENSE_MATES; i++){
        if(get_seen_status_entry(potential_id, i, &seen_status_tbl_entry_buf) == TABLE_SUCCESS){
            if(timestamp < seen_status_tbl_entry_buf.gateTime){
                timestamp = seen_status_tbl_entry_buf.gateTime;
                state = seen_status_tbl_entry_buf.status;
            }
        }
    }

    if(!success){
        return; //no seen status entry found
    }
    //check if gate already there
    if(!gate_listed(seen_status_tbl_entry_buf.gateID)){
        add_gate(&(gate_entry){
            .gate_id = seen_status_tbl_entry_buf.gateID,
            .gate_is_state = state,
            .gate_requested_state = UNKNOWN,
            .job_is_todo = false,
            .job_prio = 0,
            .sig_strength = 0
        });
    }else{
        //update is state
        set_is_state(seen_status_tbl_entry_buf.gateID, state);
    }
}

void update_with_latest_status(int potential_id){
    uint32_t timestamp = 0; 
    uint8_t state = 0;
    bool success = false;
    //get the latest seen status entry
    for (int i = 0; i < MAX_SENSE_MATES; i++){
        if(get_seen_status_entry(potential_id, i, &seen_status_tbl_entry_buf) == TABLE_SUCCESS){
            if(timestamp < (uint32_t)seen_status_tbl_entry_buf.gateTime){
                timestamp = seen_status_tbl_entry_buf.gateTime;
                state = seen_status_tbl_entry_buf.status;
                success = true;
            }
        }
    }
    if(get_is_state_entry(potential_id, &is_state_tbl_entry_buf) == TABLE_SUCCESS){
        //check if seen status is newer than is state
        if(timestamp < is_state_tbl_entry_buf.gateTime){
            state = is_state_tbl_entry_buf.state;
            success = true;
        }
    }

    if(!success){
        return; //no seen or is status entry found
    }

    //check if gate already there
    if(!gate_listed(potential_id)){
        add_gate(&(gate_entry){
            .gate_id = potential_id,
            .gate_is_state = state,
            .gate_requested_state = UNKNOWN,
            .job_is_todo = false,
            .job_prio = 0,
            .sig_strength = 0
        });
    }else{
        //update is state
        set_is_state(potential_id, state);
    }
}

void update_with_jobs(int potential_id){
    if(get_jobs_entry(potential_id, &jobs_tbl_entry_buf) == TABLE_SUCCESS){
        //check if gate already there
        if(!gate_listed(jobs_tbl_entry_buf.gateID)){
            add_gate(&(gate_entry){
                .gate_id = jobs_tbl_entry_buf.gateID,
                .gate_is_state = UNKNOWN,
                .gate_requested_state = UNKNOWN,
                .job_is_todo = jobs_tbl_entry_buf.done == JOB_IN_PROGRESS,
                .job_prio = (jobs_tbl_entry_buf.done == JOB_IN_PROGRESS ? jobs_tbl_entry_buf.priority : 0),
                .sig_strength = 0
            });
        }else{
            //update job prio and todo state
            set_job_prio(jobs_tbl_entry_buf.gateID, (jobs_tbl_entry_buf.done == JOB_IN_PROGRESS ? jobs_tbl_entry_buf.priority : 0));
            set_job_done(jobs_tbl_entry_buf.gateID, jobs_tbl_entry_buf.done);
        }
    }
}

void update_with_timestamp(int potential_id){
    //printf("Updating with timestamp for gate %d\n", potential_id);
    if(get_timestamp_entry(potential_id, &timestamp_tbl_entry_buf) == TABLE_SUCCESS){
        //check if gate already there
        if(!gate_listed(timestamp_tbl_entry_buf.gateID)){
            add_gate(&(gate_entry){
                .gate_id = timestamp_tbl_entry_buf.gateID,
                .gate_is_state = UNKNOWN,
                .gate_requested_state = UNKNOWN,
                .job_is_todo = false,
                .job_prio = 0,
                .sig_strength = timestamp_tbl_entry_buf.rssi
            });
        }else{
            //update signal strength
            set_sig_strength(timestamp_tbl_entry_buf.gateID, timestamp_tbl_entry_buf.rssi);
        }
    }
}

void update_menu_from_tables(void){
    printf("Updating menu from tables\n");
    for(int i = 0; i< MAX_GATES; i++){
        update_with_target(i);
        //update_with_is_state(i); //alternative
        //update_with_seen_status(i); //alternative
        update_with_latest_status(i); //alternative
        update_with_jobs(i);
        update_with_timestamp(i);
    }
}

/* 
    ^^^^^^^^^^^^^^^^^^^^^^^^^^^^^^
    UNTIL HERE FUNCTIONS TO WORK WITH TABLES

    ------------------------------

    FROM HERE FUNCTIONS TO WORK IN THE MENU
    vvvvvvvvvvvvvvvvvvvvvvvvvvvvvv
*/


void main_menu_entry_view(void){
    upper_entry.menu = MAIN;
    upper_entry.subentry = HEADER;
    upper_entry.current_gate = NULL;
    upper_entry.selected = false;

    lower_entry.menu = MAIN;
    lower_entry.subentry = GATES;
    lower_entry.current_gate = NULL;
    lower_entry.selected = true;
}

void init_new_menu(void){
    main_menu_entry_view();
}

void reorder_close_by(void){
    int added_cnt = 0;
    int8_t curr_sig_strength = -127;
    int8_t last_sig_strenght = 0;
    bool todo_closeby = false;
    while(added_cnt < current_num_gates && last_sig_strenght > MIN_SIGNAL_STRENGTH){
        //find sigstrenght to add
        for (int i=0; i<current_num_gates; i++){
            if(all_entries[i].sig_strength < last_sig_strenght && all_entries[i].sig_strength > curr_sig_strength){
                curr_sig_strength = all_entries[i].sig_strength;
                printf("New sig strength: %d\n", curr_sig_strength);
            }
        }
        if(curr_sig_strength < MIN_SIGNAL_STRENGTH){
            break; //no more gates to add
        }
        //add gates with sigstrengt
        for(int i=0; i<current_num_gates; i++){
            if(all_entries[i].sig_strength == curr_sig_strength){
                if(all_entries[i].job_is_todo){
                    todo_closeby = true;
                }
                close_by_order[added_cnt] = &all_entries[i];
                added_cnt += 1;
            }
        }
        last_sig_strenght = curr_sig_strength;
        curr_sig_strength = -127;
    }
    current_num_close_by = added_cnt;
    printf("Close by gates: %d\n", current_num_close_by);
    if(todo_closeby){
        event_post(&sound_queue, &close_by_todo_sound_event);
    }
}


void reorder_jobs(void){
    int added_cnt = 0;
    int curr_prio = 0;
    int last_prio = INT32_MAX;
    while(added_cnt < current_num_gates && last_prio > MIN_JOB_PRIO){
        //find sigstrenght to add
        for (int i=0; i<current_num_gates; i++){
            if(!all_entries[i].job_is_todo){
                continue;
            }
            if(all_entries[i].job_prio < last_prio && all_entries[i].job_prio > curr_prio){
                curr_prio = all_entries[i].job_prio;
            }
        }
        if(curr_prio < MIN_JOB_PRIO){
            break; //no more jobs to add
        }
        //add gates with sigstrengt
        for(int i=0; i<current_num_gates; i++){
            if(!all_entries[i].job_is_todo){
                continue;
            }
            if(all_entries[i].job_prio == curr_prio){
                jobs_order[added_cnt] = &all_entries[i];
                added_cnt += 1;
            }
        }
        last_prio = curr_prio;
        curr_prio = 0;
    }
    current_num_jobs = added_cnt;
}


void add_gate(gate_entry *new_entry){
    if(current_num_gates >= MAX_GATES){
        return;
    }
    if(new_entry == NULL){
        return;
    }

    //check if gate already there
    for (int i = 0; i < current_num_gates; i++){
        if(all_entries[i].gate_id == new_entry->gate_id){
            return;
        }
    }

    int new_idx = 0;
    bool inbetween = false;
    for (int i = current_num_gates; i > 0; i--){
        if(all_entries[i-1].gate_id > new_entry->gate_id){
            all_entries[i] = all_entries[i-1];
            inbetween = true;
        } else{
            new_idx = inbetween ? i-1: i;
            break;
        }
    }
    current_num_gates += 1;

    memcpy(&all_entries[new_idx], new_entry, sizeof(gate_entry));
    reorder_close_by();
    reorder_jobs();
}


void rm_gate(int gate_id){
    bool found_to_rm = false;
    for(int i= 0; i<current_num_gates; i++){
        if(found_to_rm && all_entries[i].gate_id > gate_id){
            all_entries[i-1] = all_entries[i];
        }else if(all_entries[i].gate_id == gate_id){
            found_to_rm = true;
        }
    }
    if(found_to_rm){
        current_num_gates -=1;
    }
}


void set_is_state(int gate_id, gate_state state){
    for(int i = 0; i< current_num_gates; i++){
        if(all_entries[i].gate_id == gate_id){
            all_entries[i].gate_is_state = state;
        }
    }
}

void set_requested_state(int gate_id, gate_state state){
    for(int i = 0; i< current_num_gates; i++){
        if(all_entries[i].gate_id == gate_id){
            all_entries[i].gate_requested_state = state;
        }
    }
}

void set_sig_strength(int gate_id, int sig_strenght){
    for(int i = 0; i< current_num_gates; i++){
        if(all_entries[i].gate_id == gate_id){
            all_entries[i].sig_strength = sig_strenght;
        }
    }
    reorder_close_by();
}


void set_job_done(int gate_id, bool done){
    for(int i = 0; i< current_num_gates; i++){
        if(all_entries[i].gate_id == gate_id){
            all_entries[i].job_is_todo = !done;
        }
    }
}


void set_job_prio(int gate_id, int new_prio){
    for(int i = 0; i< current_num_gates; i++){
        if(all_entries[i].gate_id == gate_id){
            all_entries[i].job_prio = new_prio;
        }
    }
    reorder_jobs();
}

int get_num_gates(void){
    return current_num_gates;
}

bool gate_listed(int gate_id){
    for(int i = 0; i< current_num_gates; i++){
        if(all_entries[i].gate_id == gate_id){
            return true;
        }
    }
    return false;
}

//get to gate overview menu to header
void main_to_gate_overview(void){
    upper_entry.menu = GATE_OVERVIEW;
    upper_entry.subentry = HEADER;
    upper_entry.current_gate = NULL;
    upper_entry.selected = false;

    lower_entry.menu = GATE_OVERVIEW;
    if(current_num_gates > 0){
        lower_entry.subentry = OTHER;
        lower_entry.current_gate = &all_entries[0];
    }else{
        lower_entry.subentry = CANCEL;
        lower_entry.current_gate = NULL;
    }
    lower_entry.selected = true;
}

//get back to gate overview menu to the before selected gate
void cancel_to_gate_overview(void){
    upper_entry.menu = GATE_OVERVIEW;
    upper_entry.subentry = OTHER;
    upper_entry.selected = true;

    lower_entry.menu = GATE_OVERVIEW;

    if(&all_entries[current_num_gates -1] == upper_entry.current_gate){
        lower_entry.subentry = CANCEL;
        lower_entry.current_gate = NULL;
    }else{
        lower_entry.subentry = OTHER;
        lower_entry.current_gate = upper_entry.current_gate + 1;
    }
    lower_entry.selected = false;
}

//get to job prios menu to header
void main_to_job_prios(void){
    upper_entry.menu = JOB_PRIOS;
    upper_entry.subentry = HEADER;
    upper_entry.current_gate = NULL;
    upper_entry.selected = false;

    lower_entry.menu = JOB_PRIOS;
    if(current_num_jobs > 0){
        lower_entry.subentry = OTHER;
        lower_entry.current_gate = jobs_order[0];
    }else{
        lower_entry.subentry = CANCEL;
        lower_entry.current_gate = NULL;
    }
    lower_entry.selected = true;
}

//get to close by menu to header
void main_to_close_by(void){
    upper_entry.menu = CLOSE_BY_MENU;
    upper_entry.subentry = HEADER;
    upper_entry.current_gate = NULL;
    upper_entry.selected = false;

    lower_entry.menu = CLOSE_BY_MENU;
    if(current_num_close_by > 0){
        lower_entry.subentry = OTHER;
        lower_entry.current_gate = close_by_order[0];
    }else{
        lower_entry.subentry = CANCEL;
        lower_entry.current_gate = NULL;
    }
    lower_entry.selected = true;
}

//get back to job prios menu to the before selected gate
void cancel_to_job_prios(void){
    upper_entry.menu = JOB_PRIOS;
    upper_entry.subentry = OTHER;
    upper_entry.selected = true;

    lower_entry.menu = JOB_PRIOS;

    if(current_num_jobs == 0 || upper_entry.current_gate->job_prio < MIN_JOB_PRIO){
        main_to_close_by();
        return; //no close by gates, so no lower entry
    }

    if(jobs_order[current_num_jobs -1] == upper_entry.current_gate){
        lower_entry.subentry = CANCEL;
        lower_entry.current_gate = NULL;
    
    }else{
        lower_entry.subentry = OTHER;
        for(int i = 0; i < current_num_jobs; i++){
            if(jobs_order[i] == upper_entry.current_gate){
                lower_entry.current_gate = jobs_order[i+1];
                break;
            }
        }
    }
    lower_entry.selected = false;
}

//get back to close by menu to the before selected gate
void cancel_to_close_by(void){
    upper_entry.menu = CLOSE_BY_MENU;
    upper_entry.subentry = OTHER;
    upper_entry.selected = true;
    lower_entry.menu = CLOSE_BY_MENU;

    if(current_num_close_by == 0 || upper_entry.current_gate->sig_strength < MIN_SIGNAL_STRENGTH){
        main_to_close_by();
        return; //no close by gates, so no lower entry
    }
    
    if(close_by_order[current_num_close_by-1] == upper_entry.current_gate){
        lower_entry.subentry = CANCEL;
        lower_entry.current_gate = NULL;
    
    }else{
        lower_entry.subentry = OTHER;
        for(int i = 0; i < current_num_close_by; i++){
            if(close_by_order[i] == upper_entry.current_gate){
                lower_entry.current_gate = close_by_order[i+1];
                break;
            }
        }
    }
    lower_entry.selected = false;
}


/*
    FROM HERE INPUT HANDLING FUNCTIONS
    vvvvvvvvvvvvvvvvvvvvvvvvvvvvvv
*/

void main_menu_input(input input){
    switch (input){
        case UP:
            if(upper_entry.subentry == HEADER){
                return;
            }

            if(upper_entry.selected){
                lower_entry.subentry = upper_entry.subentry;
                upper_entry.subentry -= 1;
            }else{
                upper_entry.selected = true;
                lower_entry.selected = false;
            }

            /*Header not selectable*/
            if(upper_entry.subentry == HEADER){
                upper_entry.selected = false;
                lower_entry.selected = true;
            }
        break;

        case DOWN:
            if(lower_entry.subentry == CLOSE_BY && lower_entry.selected){
                return;
            }
            if(lower_entry.selected){
                upper_entry.subentry = lower_entry.subentry;
                lower_entry.subentry += 1;
            }else{
                upper_entry.selected = false;
                lower_entry.selected = true;
            }

        break;
        
        case SELECT:
            if(upper_entry.selected){
                if(upper_entry.subentry == GATES){
                    main_to_gate_overview();
                }else if (upper_entry.subentry == JOBS){
                    main_to_job_prios();
                }else if (upper_entry.subentry == CLOSE_BY){
                    main_to_close_by();
                }
            }else{
                if(lower_entry.subentry == GATES){
                    main_to_gate_overview();
                }else if (lower_entry.subentry == JOBS){
                    main_to_job_prios();
                }else if (lower_entry.subentry == CLOSE_BY){
                    main_to_close_by();
                }
            }
        break;
    }
}


void specific_gate_selected(gate_entry *gate){
    upper_entry.menu = SELECTED_GATE;
    upper_entry.subentry = HEADER;
    upper_entry.current_gate = gate;
    upper_entry.selected = false;

    lower_entry.menu = SELECTED_GATE;
    lower_entry.subentry = MARK_OPEN;
    lower_entry.current_gate = gate;
    lower_entry.selected = true;
}

void gate_overview_input(input input){
    switch(input){
        case UP:
            if(upper_entry.subentry == HEADER){
                return;
            }

            if(lower_entry.selected){
                upper_entry.selected = true;
                lower_entry.selected = false;

            }else if(upper_entry.current_gate == &all_entries[0] && upper_entry.selected){
                upper_entry.subentry = HEADER;
                upper_entry.current_gate = NULL;
                upper_entry.selected = false;

                lower_entry.subentry = OTHER;
                lower_entry.current_gate = &all_entries[0];
                lower_entry.selected = true;

            }else{
                lower_entry.current_gate = upper_entry.current_gate;
                lower_entry.subentry = upper_entry.subentry;
                upper_entry.current_gate -= 1;
                upper_entry.subentry = OTHER;
            }
        break;
        
        case DOWN:
            if(lower_entry.subentry == CANCEL && lower_entry.selected){
                return;
            }

            if(upper_entry.selected){
                lower_entry.selected = true;
                upper_entry.selected = false;
            
            }else if(lower_entry.current_gate == &all_entries[current_num_gates - 1] && lower_entry.selected){
                lower_entry.subentry = CANCEL;
                lower_entry.current_gate = NULL;

                upper_entry.subentry = OTHER;
                upper_entry.current_gate = &all_entries[current_num_gates - 1];
                
            }else{
                upper_entry.current_gate = lower_entry.current_gate;
                upper_entry.subentry = lower_entry.subentry;
                lower_entry.current_gate += 1;
                lower_entry.subentry = OTHER;
            }
        break;

        case SELECT:
            if(upper_entry.selected && upper_entry.subentry == OTHER){
                specific_gate_selected(upper_entry.current_gate);
            }else if (lower_entry.selected && lower_entry.subentry == CANCEL){
                main_menu_entry_view();
            }else if (lower_entry.selected && lower_entry.subentry == OTHER){
                specific_gate_selected(lower_entry.current_gate);
            }
        break;

        default:
        break;
    }
}


void specific_job_selected(gate_entry *gate){
    upper_entry.menu = SELECTED_JOB;
    upper_entry.subentry = HEADER;
    upper_entry.current_gate = gate;
    upper_entry.selected = false;

    lower_entry.menu = SELECTED_JOB;
    lower_entry.subentry = MARK_OPEN;
    lower_entry.current_gate = gate;
    lower_entry.selected = true;
}

void job_prios_input(input input){
    switch (input){
    case UP:
        if(upper_entry.subentry == HEADER){
            return;
        }

        if(lower_entry.selected){
            upper_entry.selected = true;
            lower_entry.selected = false;
        }else if(upper_entry.current_gate == jobs_order[0] && upper_entry.selected){
            upper_entry.subentry = HEADER;
            upper_entry.current_gate = NULL;
            upper_entry.selected = false;
            lower_entry.subentry = OTHER;
            lower_entry.current_gate = jobs_order[0];
            lower_entry.selected = true;
        }else{
            lower_entry.current_gate = upper_entry.current_gate;
            lower_entry.subentry = upper_entry.subentry;
            for(int i = 0; i < current_num_jobs; i++){
                if(jobs_order[i] == upper_entry.current_gate){
                    upper_entry.current_gate = jobs_order[i-1];
                    break;
                }
            }
            upper_entry.subentry = OTHER;
        }
    break;
    
    case DOWN:
        if(lower_entry.subentry == CANCEL && lower_entry.selected){
            return;
        }

        if(upper_entry.selected){
            lower_entry.selected = true;
            upper_entry.selected = false;
        }else if(lower_entry.current_gate == jobs_order[current_num_jobs -1] && lower_entry.selected){
            lower_entry.subentry = CANCEL;
            lower_entry.current_gate = NULL;

            upper_entry.subentry = OTHER;
            upper_entry.current_gate = jobs_order[current_num_jobs - 1];
        }else{
            upper_entry.current_gate = lower_entry.current_gate;
            upper_entry.subentry = lower_entry.subentry;
            for(int i = 0; i < current_num_jobs; i++){
                if(jobs_order[i] == lower_entry.current_gate){
                    lower_entry.current_gate = jobs_order[i+1];
                    break;
                }
            }
            lower_entry.subentry = OTHER;
        }
    break;

    case SELECT:
        if(upper_entry.selected && upper_entry.subentry == OTHER){
            specific_job_selected(upper_entry.current_gate);
        }
        else if (lower_entry.selected && lower_entry.subentry == CANCEL){
            main_menu_entry_view();
        }else if (lower_entry.selected && lower_entry.subentry == OTHER){
            specific_job_selected(lower_entry.current_gate);
        }
    default:
        break;
    }
}


void specific_close_by_selected(gate_entry *gate){
    upper_entry.menu = SELECTED_CLOSE_BY;
    upper_entry.subentry = HEADER;
    upper_entry.current_gate = gate;
    upper_entry.selected = false;

    lower_entry.menu = SELECTED_CLOSE_BY;
    lower_entry.subentry = MARK_OPEN;
    lower_entry.current_gate = gate;
    lower_entry.selected = true;
}

void close_by_input(input input){
    switch (input){
    case UP:
        if(upper_entry.subentry == HEADER){
            return;
        }

        if(lower_entry.selected){
            upper_entry.selected = true;
            lower_entry.selected = false;
        }else if(upper_entry.current_gate == close_by_order[0] && upper_entry.selected){
            upper_entry.subentry = HEADER;
            upper_entry.current_gate = NULL;
            upper_entry.selected = false;
            lower_entry.subentry = OTHER;
            lower_entry.current_gate = close_by_order[0];
            lower_entry.selected = true;
        }else{
            lower_entry.current_gate = upper_entry.current_gate;
            lower_entry.subentry = upper_entry.subentry;
            for(int i = 0; i < current_num_close_by; i++){
                if(close_by_order[i] == upper_entry.current_gate){
                    upper_entry.current_gate = close_by_order[i-1];
                    break;
                }
            }
            upper_entry.subentry = OTHER;
        }
    break;
    
    case DOWN:
        if(lower_entry.subentry == CANCEL && lower_entry.selected){
            return;
        }

        if(upper_entry.selected){
            lower_entry.selected = true;
            upper_entry.selected = false;
        }else if(lower_entry.current_gate == close_by_order[current_num_close_by -1] && lower_entry.selected){
            lower_entry.subentry = CANCEL;
            lower_entry.current_gate = NULL;

            upper_entry.subentry = OTHER;
            upper_entry.current_gate = close_by_order[current_num_close_by - 1];
        }else{
            upper_entry.current_gate = lower_entry.current_gate;
            upper_entry.subentry = lower_entry.subentry;
            for(int i = 0; i < current_num_close_by; i++){
                if(close_by_order[i] == lower_entry.current_gate){
                    lower_entry.current_gate = close_by_order[i+1];
                    break;
                }
            }
            lower_entry.subentry = OTHER;
        }
    break;

    case SELECT:
        if(upper_entry.selected && upper_entry.subentry == OTHER){
            specific_close_by_selected(upper_entry.current_gate);
        }
        else if (lower_entry.selected && lower_entry.subentry == CANCEL){
            main_menu_entry_view();
        }else if (lower_entry.selected && lower_entry.subentry == OTHER){
            specific_close_by_selected(lower_entry.current_gate);
        }
    default:
        break;
    }
}

void to_confirmation_open(menu_type menu){
    upper_entry.selected = false;
    lower_entry.selected = true;
    upper_entry.subentry = HEADER;
    lower_entry.subentry = CONFIRM;
    switch (menu){
        case SELECTED_GATE:
            upper_entry.menu = CONFIRMATION_GATE_OPEN;
            lower_entry.menu = CONFIRMATION_GATE_OPEN;
        break;

        case SELECTED_JOB:
            upper_entry.menu = CONFIRMATION_JOB_OPEN;
            lower_entry.menu = CONFIRMATION_JOB_OPEN;
        break;

        case SELECTED_CLOSE_BY:
            upper_entry.menu = CONFIRMATION_CLOSE_BY_OPEN;
            lower_entry.menu = CONFIRMATION_CLOSE_BY_OPEN;
        break;

        default:
        break;
    }
}

void to_confirmation_closed(menu_type menu){
    upper_entry.selected = false;
    lower_entry.selected = true;
    upper_entry.subentry = HEADER;
    lower_entry.subentry = CONFIRM;
    switch (menu){
        case SELECTED_GATE:
            upper_entry.menu = CONFIRMATION_GATE_CLOSE;
            lower_entry.menu = CONFIRMATION_GATE_CLOSE;
        break;

        case SELECTED_JOB:
            upper_entry.menu = CONFIRMATION_JOB_CLOSE;
            lower_entry.menu = CONFIRMATION_JOB_CLOSE;
        break;

        case SELECTED_CLOSE_BY:
            upper_entry.menu = CONFIRMATION_CLOSE_BY_CLOSE;
            lower_entry.menu = CONFIRMATION_CLOSE_BY_CLOSE;
        break;

        default:
        break;
    }
}

void selected_input(input input, menu_type menu){
    switch (input){
        case UP:
            if(upper_entry.subentry == HEADER){
                return;
            }

            if(lower_entry.selected){
                upper_entry.selected = true;
                lower_entry.selected = false;
            } else if(upper_entry.selected && upper_entry.subentry == MARK_OPEN){
                upper_entry.subentry = HEADER;
                upper_entry.selected = false;
                lower_entry.subentry = MARK_OPEN;
                lower_entry.selected = true;
            }else{
                lower_entry.subentry = upper_entry.subentry;
                upper_entry.subentry -= 1;
            }
        break;

        case DOWN:
            if(lower_entry.subentry == CANCEL && lower_entry.selected){
                return;
            }

            if(upper_entry.selected){
                lower_entry.selected = true;
                upper_entry.selected = false;
            }else{
                upper_entry.subentry = lower_entry.subentry;
                lower_entry.subentry += 1;
            }
        break;

        case SELECT:
            if(upper_entry.selected){
                if(upper_entry.subentry == MARK_OPEN){
                    to_confirmation_open(menu);

                }else if (upper_entry.subentry == MARK_CLOSED){
                    to_confirmation_closed(menu);

                }else if (upper_entry.subentry == CANCEL){
                    if(menu == SELECTED_GATE){
                        cancel_to_gate_overview();
                        
                    }else if (menu == SELECTED_JOB){
                        cancel_to_job_prios();

                    }else if (menu == SELECTED_CLOSE_BY){
                        cancel_to_close_by();
                    }
                }
            }else{
                if(lower_entry.subentry == MARK_OPEN){
                    to_confirmation_open(menu);

                }else if (lower_entry.subentry == MARK_CLOSED){
                    to_confirmation_closed(menu);

                }else if (lower_entry.subentry == CANCEL){
                    if(menu == SELECTED_GATE){
                        cancel_to_gate_overview();
                        
                    }else if (menu == SELECTED_JOB){
                        cancel_to_job_prios();

                    }else if (menu == SELECTED_CLOSE_BY){
                        cancel_to_close_by();
                    }
                }
            }
    }
}


void confirmation_open_closed(input input, menu_type menu, gate_state state){
    switch (input){
        case UP:
            if(upper_entry.subentry == HEADER){
                return;
            }

            if(lower_entry.selected){
                upper_entry.selected = true;
                lower_entry.selected = false;
            }else if (upper_entry.subentry == CONFIRM){
                lower_entry.subentry = upper_entry.subentry;
                upper_entry.subentry = HEADER;
            }
        break;

        case DOWN:
            if(lower_entry.subentry == CANCEL && lower_entry.selected){
                return;
            }

            if(upper_entry.selected){
                lower_entry.selected = true;
                upper_entry.selected = false;
            }else if (lower_entry.subentry == CONFIRM){
                upper_entry.subentry = lower_entry.subentry;
                lower_entry.subentry = CANCEL;
            }
        break;
            
        case SELECT:
            if(upper_entry.selected && upper_entry.subentry == CONFIRM){
                
                if(state == OPEN){
                    set_is_state(upper_entry.current_gate->gate_id, OPEN);
                    in_tables_set_gate_open_closed(upper_entry.current_gate->gate_id, OPEN);
                }else if (state == CLOSED){
                    set_is_state(upper_entry.current_gate->gate_id, CLOSED);
                    in_tables_set_gate_open_closed(upper_entry.current_gate->gate_id, CLOSED);
                }
                
                if(upper_entry.current_gate->gate_is_state == upper_entry.current_gate->gate_requested_state){
                    set_job_done(upper_entry.current_gate->gate_id, true);
                    in_tables_set_gate_job_done(upper_entry.current_gate->gate_id, true);
                }
                event_post(EVENT_PRIO_MEDIUM, &send_is_state_table);
                event_post(EVENT_PRIO_MEDIUM, &send_seen_status_table);
            } else if (lower_entry.selected && lower_entry.subentry == CONFIRM){

                if(state == OPEN){
                    set_is_state(lower_entry.current_gate->gate_id, OPEN);
                    in_tables_set_gate_open_closed(lower_entry.current_gate->gate_id, OPEN);
                }else if (state == CLOSED){
                    set_is_state(lower_entry.current_gate->gate_id, CLOSED);
                    in_tables_set_gate_open_closed(lower_entry.current_gate->gate_id, CLOSED);
                }
                
                if(lower_entry.current_gate->gate_is_state == lower_entry.current_gate->gate_requested_state){
                    set_job_done(lower_entry.current_gate->gate_id, true);
                    in_tables_set_gate_job_done(lower_entry.current_gate->gate_id, true);
                }
                event_post(EVENT_PRIO_MEDIUM, &send_is_state_table);
                event_post(EVENT_PRIO_MEDIUM, &send_seen_status_table);
            }

            if(menu == CONFIRMATION_GATE_OPEN || menu == CONFIRMATION_GATE_CLOSE){
                cancel_to_gate_overview();
            }else if (menu == CONFIRMATION_JOB_OPEN || menu == CONFIRMATION_JOB_CLOSE){
                cancel_to_job_prios();
            }else if (menu == CONFIRMATION_CLOSE_BY_OPEN || menu == CONFIRMATION_CLOSE_BY_CLOSE){
                cancel_to_close_by();
            }
        break; 
    }
}



void menu_input(input input){
    switch (upper_entry.menu){
        case MAIN:
            main_menu_input(input);
        break;

        case GATE_OVERVIEW:
            gate_overview_input(input);
        break;

        case JOB_PRIOS:
            job_prios_input(input);
        break;

        case CLOSE_BY_MENU:
            close_by_input(input);
        break;

        case SELECTED_GATE:
            selected_input(input, SELECTED_GATE);
        break;

        case CONFIRMATION_GATE_OPEN:
            confirmation_open_closed(input, CONFIRMATION_GATE_OPEN, OPEN);
        break;

        case CONFIRMATION_GATE_CLOSE:
            confirmation_open_closed(input, CONFIRMATION_GATE_CLOSE, CLOSED);
        break;

        case SELECTED_JOB:
            selected_input(input, SELECTED_JOB);
        break;

        case CONFIRMATION_JOB_OPEN:
            confirmation_open_closed(input, CONFIRMATION_JOB_OPEN, OPEN);
        break;

        case CONFIRMATION_JOB_CLOSE:
            confirmation_open_closed(input, CONFIRMATION_JOB_CLOSE, CLOSED);
        break;

        case SELECTED_CLOSE_BY:
            selected_input(input, SELECTED_CLOSE_BY);
        break;

        case CONFIRMATION_CLOSE_BY_OPEN:
            confirmation_open_closed(input, CONFIRMATION_CLOSE_BY_OPEN, OPEN);
        break;

        case CONFIRMATION_CLOSE_BY_CLOSE:
            confirmation_open_closed(input, CONFIRMATION_CLOSE_BY_CLOSE, CLOSED);
        break;

        default:
        break;
    }
    update_menu_display();
}



/*
    FROM HERE FUNCTIONS TO DISPLAY THE MENU
    vvvvvvvvvvvvvvvvvvvvvvvvvvvvvv
*/

void display_header(display_entry *entry){
    if(entry == NULL){
        return;
    }

    switch(entry->menu){
        case MAIN:
            display_menu_header("SenseMate ID ", SENSEMATE_ID, true);
            break;
        case GATE_OVERVIEW:
            display_menu_header("All Gates: ", current_num_gates, true);
            break;
        case JOB_PRIOS:
            display_menu_header("Jobs: ", current_num_jobs, true);
            break;
        case CLOSE_BY_MENU:
            display_menu_header("Close By: ", current_num_close_by, true);
            break;
        case SELECTED_GATE:
        case SELECTED_JOB:
        case SELECTED_CLOSE_BY:
            display_menu_header("set Gate: ", entry->current_gate->gate_id, true);
            break;
        case CONFIRMATION_GATE_OPEN:
        case CONFIRMATION_JOB_OPEN:
        case CONFIRMATION_CLOSE_BY_OPEN:
            display_menu_header("Open Gate: ", entry->current_gate->gate_id, true);
            break;
        case CONFIRMATION_GATE_CLOSE:
        case CONFIRMATION_JOB_CLOSE:
        case CONFIRMATION_CLOSE_BY_CLOSE:
            display_menu_header("Close Gate: ", entry->current_gate->gate_id, true);
            break;
        default:
            printf("display_header: Unknown menu type %d\n", entry->menu);
            break;

    }
}

void display_main(display_entry *entry, bool upper){
    char *text = NULL;
    bool more_content = false;
    int displayed_num = 0;
    bool use_num = true;
    switch (entry->subentry){
        case GATES:
            text = "All Gates: ";
            displayed_num = current_num_gates;
            more_content = !upper;
            break;
        case JOBS:
            text = "Jobs: ";
            displayed_num = current_num_jobs;
            more_content = true;
            break;
        case CLOSE_BY:
            text = "Close By: ";
            displayed_num = current_num_close_by;
            break;
        default:
            printf("display_main: Unknown subentry type %d\n", entry->subentry);
            text = "ERROR IN CODE";
            use_num = false;
            break;
    }

    display_ordinary_menu(text, displayed_num, use_num, upper, entry->selected, more_content);
}

void display_gate(display_entry *entry, bool upper){
    if(entry->subentry == CANCEL){
        display_ordinary_menu("cancel", 0, false, upper, entry->selected, false);
        return;
    }
    uint8_t job_prio = 0;
    if(entry->current_gate->job_is_todo){
        job_prio = entry->current_gate->job_prio;
    }
    display_gate_menu_box("Gate ", //text
            entry->current_gate->gate_id, //num_after_text
            upper, //if upper
            entry->selected, // if selected
            entry->current_gate->gate_is_state == OPEN, // gate_state_open
            entry->current_gate->gate_requested_state == entry->current_gate->gate_is_state, // requested_match
            job_prio, // job_prio
            (!upper || (entry->current_gate->gate_id != all_entries[0].gate_id)) // if more content
        );
}

void display_selected(display_entry *entry, bool upper){
    char *text = NULL;
    bool more_content = false;
    switch(entry->subentry){
        case MARK_OPEN:
            text = "seen open";
            if(!upper){
                more_content = true;
            }
            break;
        case MARK_CLOSED:
            text = "seen closed";
            more_content = true;
            break;
        case CANCEL:
            text = "cancel";
            break;
        default:
            printf("display_selected: Unknown subentry type %d\n", entry->subentry);
            text = "ERROR IN CODE";
            return;
    }
    display_ordinary_menu(text, 0, false, upper, entry->selected, more_content);
}

void display_confirmation(display_entry *entry, bool upper){
    char *text = NULL;
    bool more_content = false;
    switch(entry->subentry){
        case CONFIRM:
            text = "confirm";
            if(!upper){
                more_content = true;
            }
            break;
        case CANCEL:
            text = "cancel";
            break;
        default:
            printf("display_confirmation: Unknown subentry type %d\n", entry->subentry);
            text = "ERROR IN CODE";
            return;
    }
    display_ordinary_menu(text, 0, false, upper, entry->selected, more_content);
}

void update_menu_display(void){
    new_page();

    if(upper_entry.subentry == HEADER){
        display_header(&upper_entry);
    }else if(upper_entry.menu == MAIN){
        display_main(&upper_entry, true);
    }else if(upper_entry.menu == GATE_OVERVIEW || upper_entry.menu == JOB_PRIOS || upper_entry.menu == CLOSE_BY_MENU){
        display_gate(&upper_entry, true);
    }else if(upper_entry.menu == SELECTED_GATE || upper_entry.menu == SELECTED_JOB || upper_entry.menu == SELECTED_CLOSE_BY){
        display_selected(&upper_entry, true);
    }else{
        display_confirmation(&upper_entry, true);
    }

    if(lower_entry.menu == MAIN){
        display_main(&lower_entry, false);
    }else if(lower_entry.menu == GATE_OVERVIEW || lower_entry.menu == JOB_PRIOS || lower_entry.menu == CLOSE_BY_MENU){
        display_gate(&lower_entry, false);
    }else if(lower_entry.menu == SELECTED_GATE || lower_entry.menu == SELECTED_JOB || lower_entry.menu == SELECTED_CLOSE_BY){
        display_selected(&lower_entry, false);
    }else{
        display_confirmation(&lower_entry, false);
    }
}
