smartuni/riot-po-2025/server/backend/src/main/java/com/riot/matesense/service/AuthService.java

package com.riot.matesense.service;

import com.riot.matesense.entity.UserEntity;
import com.riot.matesense.model.AuthRequest;
import com.riot.matesense.model.RegisterRequest;
import com.riot.matesense.model.UserChangeRequest;
import com.riot.matesense.model.AuthResponse;
import com.riot.matesense.model.UserDetailsResponse;
import com.riot.matesense.repository.UserRepository;

import io.jsonwebtoken.Claims;
import io.jsonwebtoken.Jwts;
import io.jsonwebtoken.security.Keys;

import org.springframework.beans.factory.annotation.Autowired;
import org.springframework.stereotype.Service;
import org.springframework.security.crypto.bcrypt.BCryptPasswordEncoder;

import java.security.Key;
import java.util.Date;
import java.util.HashMap;

@Service
public class AuthService {

    @Autowired
    private UserRepository userRepository;

    private HashMap<String, Long> tokenStore = new HashMap<>();

    // same secret key as the JwtService file that validates the key
    private final String secret = "12345678901234567890123456789012";
    private Key secretKey = Keys.hmacShaKeyFor(secret.getBytes());

    public AuthResponse handleLogin(AuthRequest request) {
        UserEntity user = userRepository.findByEmail(request.getEmail());

        if (user == null || !(new BCryptPasswordEncoder().matches(request.getPassword(), user.getPassword()))) {
            throw new RuntimeException("Invalid credentials");
        }

        String token = generateToken(user.getId());
        tokenStore.put(token, user.getId());
        // System.out.println("Created Login Token " + token);
        return new AuthResponse(token);
    }

    public AuthResponse handleRegister(RegisterRequest request) {
        if (userRepository.findByEmail(request.getEmail()) != null) {
            throw new RuntimeException("Email already in use");
        }
        String hashedPassword = new BCryptPasswordEncoder().encode(request.getPassword());

        UserEntity user = new UserEntity(request.getEmail(), hashedPassword, request.getName(), request.getRole());
        userRepository.save(user);

        String token = generateToken(user.getId());
        tokenStore.put(token, user.getId());
        // System.out.println("Created Register Token " + token);
        return new AuthResponse(token);
    }

    public void handleLogout(String token) {
        String splitTok = token.split(" ")[1];
        tokenStore.remove(splitTok);
        // System.out.println(tokenStore);
        // System.out.println("Logged out token: " + token);
    }

    public Long getUserIdFromToken(String token) {
        Claims claims = Jwts.parserBuilder()
                .setSigningKey(secretKey)
                .build()
                .parseClaimsJws(token)
                .getBody();
        return Long.parseLong(claims.getSubject());
    }

    public UserDetailsResponse getUserDetails(String token) {
        String splitTok = token.split(" ")[1];
        Long uId = getUserIdFromToken(splitTok);
        UserEntity user = userRepository.getById(uId);
        // System.out.println(user.getEmail());
        return new UserDetailsResponse(user.getName(), user.getEmail(), user.getRole(), user.getId());
    }

    public void changeUserDetails(UserChangeRequest request, String token) {
        String splitTok = token.split(" ")[1];
        Long uId = getUserIdFromToken(splitTok);
        UserEntity user = userRepository.getById(uId);
        if (user == null || !(new BCryptPasswordEncoder().matches(request.getPassword(), user.getPassword()))) {
            throw new RuntimeException("Invalid credentials");
        }
        if (!user.getName().equals(request.getName())) {
            user.setName(request.getName());
        }
        if (request.getNewPassword() != null && !request.getNewPassword().isBlank()) {
            if (!(new BCryptPasswordEncoder().matches(request.getNewPassword(), user.getPassword()))) {
                String hashedNewPassword = new BCryptPasswordEncoder().encode(request.getNewPassword());
                user.setPassword(hashedNewPassword);
            }
        }

        userRepository.save(user);
    }

    public String generateToken(Long userId) {
        long expirationMillis = 1000 * 60 * 60 * 24; // 24 hours
        Date now = new Date();
        Date expiryDate = new Date(now.getTime() + expirationMillis);

        return Jwts.builder()
                .setSubject(String.valueOf(userId))
                .setIssuedAt(now)
                .setExpiration(expiryDate)
                .signWith(secretKey)
                .compact();
    }
}
