smartuni/riot-po-2025/server/backend/src/main/java/com/riot/matesense/config/SecurityConfig.java

package com.riot.matesense.config;

import jakarta.servlet.http.HttpServletResponse;
import com.riot.matesense.security.JwtAuthenticationFilter;
import org.springframework.context.annotation.Bean;
import org.springframework.context.annotation.Configuration;
import org.springframework.security.config.annotation.web.builders.HttpSecurity;
import org.springframework.security.config.annotation.web.configuration.EnableWebSecurity;
import org.springframework.security.crypto.bcrypt.BCryptPasswordEncoder;
import org.springframework.security.web.SecurityFilterChain;
import org.springframework.security.web.authentication.UsernamePasswordAuthenticationFilter;
import org.springframework.web.cors.CorsConfiguration;
import org.springframework.web.cors.CorsConfigurationSource;
import org.springframework.web.cors.UrlBasedCorsConfigurationSource;

import java.util.List;

@Configuration
@EnableWebSecurity
public class SecurityConfig {

    private final JwtAuthenticationFilter jwtFilter;

    public SecurityConfig(JwtAuthenticationFilter jwtFilter) {
        this.jwtFilter = jwtFilter;
    }

    @Bean
    public SecurityFilterChain securityFilterChain(HttpSecurity http) throws Exception {
        return http
                .cors()
                .and()
                .csrf().disable()
                .authorizeHttpRequests(auth -> auth
                    // .anyRequest().permitAll()
                    .requestMatchers("/auth/**").permitAll()
                    .requestMatchers("/gates").permitAll()
                    .requestMatchers("/gate-activities").permitAll()
                    .requestMatchers("/ws/**").permitAll()
                    .anyRequest().authenticated()
                )
                .addFilterBefore(jwtFilter, UsernamePasswordAuthenticationFilter.class)
                .exceptionHandling(exception -> exception
                        .authenticationEntryPoint((request, response, authException) -> {
                            response.setStatus(HttpServletResponse.SC_UNAUTHORIZED);
                            response.getWriter().write("Unauthorized");
                        })
                )
                .build();
    }

    @Bean
    public CorsConfigurationSource corsConfigurationSource() {
        CorsConfiguration config = new CorsConfiguration();
        config.setAllowedOriginPatterns(List.of("http://localhost:3000"));
        config.setAllowedMethods(List.of("GET", "POST", "PUT", "DELETE", "OPTIONS"));
        config.setAllowedHeaders(List.of("*"));
        config.setAllowCredentials(true);

        UrlBasedCorsConfigurationSource source = new UrlBasedCorsConfigurationSource();
        source.registerCorsConfiguration("/**", config);
        return source;
    }

    @Bean
    public BCryptPasswordEncoder passwordEncoder() {
        return new BCryptPasswordEncoder();
    }
}
